sparkfun/SparkFun_GNSS_Flex_System/flex_boards/SparkPNT_GNSS_Flex_Module_LG580P/docs/software_overview.md

## QGNSS Software
!!! warning "Windows Only"
	Currently, the QGNSS software is only available for Windows operating systems.

QGNSS is highly intuitive GNSS evaluation software that is easy to use, personalized, and compatible with leading Quectel technologies. The software allows users to define or apply GNSS product configurations for specific use cases. Saving, restoring, or sharing configurations between different products and users is easy. The software supports product evaluation with a choice of views to observe static and dynamic behavior of the connected a Quectel GNSS receiver.

<article style="text-align: center;" markdown>
[:octicons-download-16:{ .heart } Download the QGNSS Software *(v2.x)* from Quectel](https://www.quectel.com/download/qgnss_v2-0_en/){ .md-button .md-button--primary target="blank" }
</article>

!!! info "System Requirements"
	**Operating System:** Windows

### Connecting to the LG580P
In order to connect to the LG580P properly, users will need to specify the settings of the UART port.

<figure markdown>
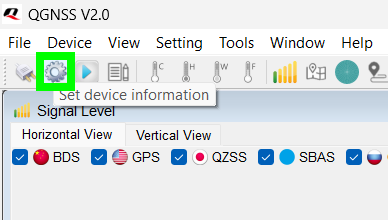
[picture p170: flex_boards/SparkPNT_GNSS_Flex_Module_LG580P/docs/assets/img/hookup_guide/qgnss-uart_settings-button.png]
Configure UART Settings

<figcaption markdown>Click the <kbd>:material-cog:</kbd> button to configure the UART settings.</figcaption>
</figure>

Before users can connect to the LG580P GNSS Flex module, they will need to specify the connection settings in QGNSS. Once configured, users can select the ++"OK"++ button and QGNSS will automatically attempt to connect to the GNSS receiver.

- Select the `LG580P(03)` from the drop-down menu to configure the `Model` of the GNSS receiver being connected.
- Below, is a list of the default settings for `UART` ports of the LG580P. These settings should be selected in the `Device Information` menu, unless configured differently.
- For the `Port`, select the port associated with the connected USB-to-Serial converter.

<figure markdown>
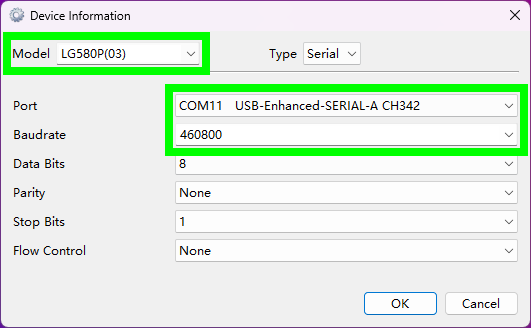
[picture p171: flex_boards/SparkPNT_GNSS_Flex_Module_LG580P/docs/assets/img/hookup_guide/qgnss-uart_settings.png]
UART Settings in QGNSS

<figcaption markdown>Specify the settings for the UART port in QGNSS.</figcaption>
</figure>

### Configure the LG580P
By default, the UART ports are configured to transmit and receive `NMEA 0183` and/or `RTCM 3.x` messages. These messages are generally used for transmitting PNT data; and providing or receiving RTK corrections, respectively. Quectel also implements a system of proprietary messages (`PQTM`) for users to configure the LG580P, following the data format of the `NMEA` protocol.

???+ terminal "Data Format - PQTM Messages"
	The expected structure of the data in the proprietary PQTM messages is shown below:

	<figure markdown>
	NMEA data structure
	<figcaption markdown>The data structure of Quectel messages for the `NMEA` protocol.</figcaption>
	</figure>

	`<Checksum>`:

	- Checksum field follows the checksum delimiter character `*`.
	- Checksum is the 8-bit exclusive OR of all characters in the sentence, including `,` the field delimiter, between but not including the `$` and the `*` delimiters.

	`<CR>` & `<LF>`: Carriage return; followed by a new line

	- Depending on the terminal emulator, these may be options configured in the program settings.
	- Otherwise, users may need to add the `\r` and `\n` characters at the end of the message.

In the QGNSS software, users can click on the ++"Advance"++ button, at the bottom of the `QConsole` window, to configure the settings for the messages sent to the LG580P. Selecting `NMEA` and `CRLF` from the drop-down menu of the **Checksum Type** and **Suffix** options, will automatically calculate and append the `<checksum>` value, carriage return, and line follow to the end of the message entered in the **Data Input** field.

<figure markdown>
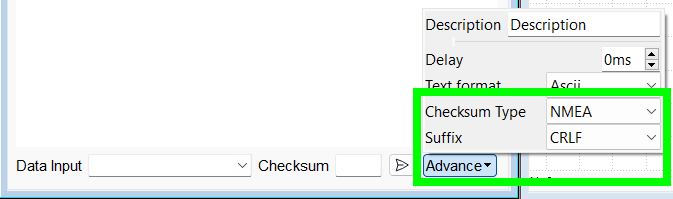
[picture p172: flex_boards/SparkPNT_GNSS_Flex_Module_LG580P/docs/assets/img/hookup_guide/qgnss-message_settings.png]
NMEA message setting

<figcaption markdown>The settings for the messages transmitted from the QConsole.</figcaption>
</figure>

???+ tip "Display the QConsole Toolbar"
	There is a toolbar for the QConsole, which has a bunch of tools that users may find useful. This includes, a search function, scroll-lock button, pause/clear the message feed, etc. To open/close the toolbar inside the QConsole, ++"right-click"++ on the mouse and select the `Show Tool` option from the drop-down menu or utilize the keyboard shortcut: ++ctrl++ + ++q++.

	<figure markdown>
	QConsole Toolbar
	<figcaption markdown>++"Right-click"++ on the mouse and select the `Show Tool` option, inside the QConsole.</figcaption>
	</figure>

??? example "Example - `PQTMCFGUART` Message"
	As an example, try utilizing the `PQTMCFGUART` PQTM message. Enter `$PQTMCFGUART,R*` into the **Data Input** field of the QConsole. DOn't forget to select the `NMEA` and `CRLF` options from ++"Advance"++ settings menu. If entered and configured properly, the value `36` should pop up in the **Checksum** field of the QConsole; then, click on the <kbd>:material-send:</kbd> button to send the message.

	``` bash
	$PQTMCFGUART,R*
	```

	Once the message has been sent, keep a close watch of the messages in the console. It may help to click on the <kbd>:octicons-unlock-16:</kbd> button to disable auto-scrolling, when trying to locate the message response. Additionally, the response may not appear right away, it could be appended to the end of the next data packet, as shown in the image below.

	<figure markdown>
	PQTM demo
	<figcaption markdown>Example of utilizing the Quectel PQTM messages in the QConsole.</figcaption>
	</figure>

### Firmware Update
In the event that users need to update the firmware on the LG580P module, please refer to the instructions in Quectel's [reference manual](./assets/component_documentation/quectel_lg290p03lgx80p03_firmware_upgrade_guide_v1-1.pdf). For the latest firmware, users should reach out to Quectel through their [forum page](https://forums.quectel.com/).

<article style="text-align: center;" markdown>

[Firmware Upgrade Manual](./assets/component_documentation/quectel_lg290p03lgx80p03_firmware_upgrade_guide_v1-1.pdf){ .md-button .md-button--primary target="blank" }

</article>

!!! warning "Synchronization Step"
	In the [reference manual](./assets/component_documentation/quectel_lg290p03lgx80p03_firmware_upgrade_guide_v1-1.pdf), **Step 9** instructs users to wait for a synchronization process. If users refer to an earlier section of the manual, this process requires the LG580P module to receive a `SYNC_WORD1` within 500ms of powering up. Therefore, users must restart the module during the synchronization step. In the QGNSS software *(+v2.1)*, this can be performed with the :material-refresh: reboot button.

	<figure markdown>
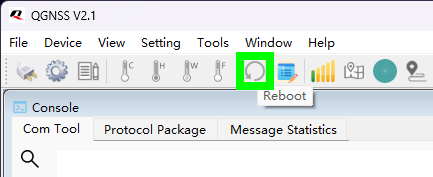
[picture p173: flex_boards/SparkPNT_GNSS_Flex_Module_LG580P/docs/assets/img/hookup_guide/qgnss-reboot_button.png]
Reboot button
	
	<figcaption markdown>Reboot button in the QGNSS software *(v2.1)*.</figcaption>
	</figure>

!!! example "Example - Step-by-Step Instructions"

	1. [Connect to the LG580P](#connecting-to-the-lg580p)
	1. From the **Tools** drop down menu, select **Firmware Update**

		**Tools** > **Firmware Update**

	1. Click the :material-file-send: button to select the receiver firmware
	1. Click to choose the firmware upgrade package whose name is identifiable by the presence of `*.pkg` file extension
	1. Click on the :fontawesome-solid-rotate-backward: button to reboot the GNSS receiver
	1. Click the :material-play: button to start the firmware upgrade process and wait for it to complete
		1. If the GNSS receiver wasn't rebooted prior initializing the upgrade, the process will wait for the synchronization step. The user will then have 20 seconds to manually reboot the GNSS receiver; otherwise, the firmware upgrade process will fail.
		1. Wait for the process to complete
	1. After the firmware upgrade is complete, the module will automatically reboot

## PyGPSClient
As an alternative to QGNSS, we recommend [PyGPSClient](https://github.com/semuconsulting/PyGPSClient) for users with computers that run on MacOS or Linux.

??? info "Resources"
	For additional information, users can refer to the following resources for the PyGPSClient software:

	- :material-github: [GitHub Repository](https://github.com/semuconsulting/PyGPSClient)
	- [Installation Instructions](https://github.com/semuconsulting/PyGPSClient?tab=readme-ov-file#installation)
	- [LG580P Configuration](https://github.com/semuconsulting/PyGPSClient?tab=readme-ov-file#nmeaconfig)
	- [PyPI Project](https://pypi.org/project/pygpsclient/)

### Installation
There are a variety of [installation methods](https://github.com/semuconsulting/PyGPSClient?tab=readme-ov-file#installation) detailed in the GitHub repository's `README.md` file. However, we recommend utilizing the `pip` installation method.

!!! terminal "Installation Commands"
	Depending on how Python is installed on the computer, one of the following commands should allow users to install the software.

	- 
		``` bash
		python3 -m pip install pygpsclient
		```
	- 
		``` bash
		pip install pygpsclient
		```

	??? info "System Requirements"
		This installation method requires an internet connection. Additionally, users will also need administrative privileges *(or root access `sudo`)* for the installation.

### Connecting to the LG580P
Before users can connect to the LG580P GNSS Flex module, they will need to specify the settings of the UART port in PyGPSClient. Once configured, users can select the <kbd>:material-usb:</kbd> button and PyGPSClient will automatically attempt to connect to the GNSS receiver.

- For the `Serial Port`, select the port associated with the GNSS receiver.

<figure markdown>
UART Settings in PyGPSClient
<figcaption markdown>Specify the settings for the UART port in QGNSS.</figcaption>
</figure>

### Terminal Emulator
Another viable option for connecting to the LG580P GNSS Flex module, is to utilize a [terminal emulation program](https://learn.sparkfun.com/tutorials/112). While reading the data sent from the LG580P is relatively trivial, users will need to be more selective when choosing an emulator to configure the LG580P GNSS receiver. This is due to the unique data structure of the proprietary messages that Quectel implements to configure the LG580P *(see the [**Configure the LG580P**](#configure-the-lg580p) section, above)*.

## Arduino Library
The [SparkFun LG290P Quadband RTK GNSS Arduino Library](https://github.com/sparkfun/SparkFun_LG290P_GNSS_Arduino_Library) can be installed from the library manager in the Arduino IDE by searching for:

	SparkFun LG290P Quadband RTK GNSS Arduino Library

<div class="grid" markdown>

<div markdown>

<figure markdown>
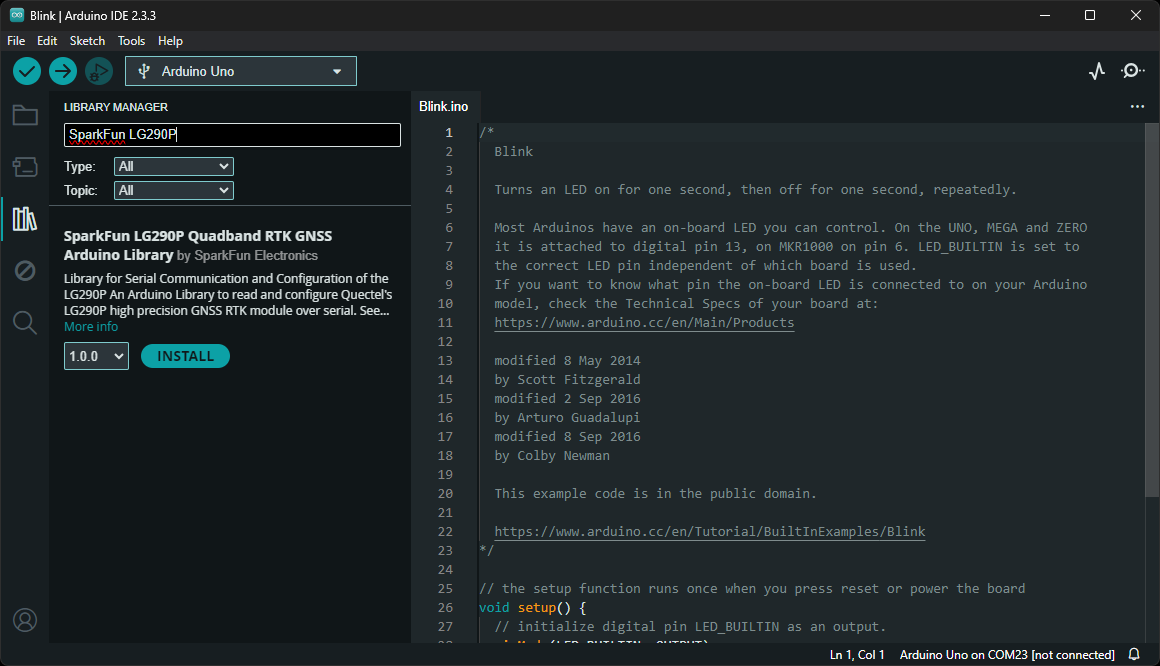
[picture p174: flex_boards/SparkPNT_GNSS_Flex_Module_LG580P/docs/assets/img/hookup_guide/arduino_library.png]
Library listed in the library manager of the Arduino IDE Click to enlarge

<figcaption markdown>The SparkFun LG290P Quadband RTK GNSS Arduino Library in the library manager of the Arduino IDE.</figcaption>
</figure>

</div>

<div markdown>

!!! tip "Manually Download the Arduino Library"
	For users who would like to manually download and install the library, the `*.zip` file can be accessed from the [GitHub repository](https://github.com/sparkfun/SparkFun_LG290P_GNSS_Arduino_Library) or downloaded by clicking the button below.

	<article style="text-align: center;" markdown>
	[:octicons-download-16:{ .heart } Download the Arduino Library](https://github.com/sparkfun/SparkFun_LG290P_GNSS_Arduino_Library/archive/refs/heads/main.zip){ .md-button .md-button--primary }
	</article>

</div>

</div>
