sparkfun/SparkFun_GNSS_Flex_System/docs/modules.md

# All Variants

<!-- Import the component -->
<script type="module" src="https://ajax.googleapis.com/ajax/libs/model-viewer/4.0.0/model-viewer.min.js"></script>

## GNSS *(only)* Modules

<div class="grid cards" style="grid-template-columns: repeat(auto-fit,minmax(8rem,1fr));" markdown>

- **SparkPNT GNSS Flex Module - mosaic-X5**

	---

	<model-viewer src="../SparkPNT_GNSS_Flex_Module_mosaic-X5/assets/3d_model/web_model.glb" camera-controls poster="../SparkPNT_GNSS_Flex_Module_mosaic-X5/assets/3d_model/poster.png" tone-mapping="neutral" shadow-intensity="2" shadow-softness="0.2" camera-orbit="0deg 75deg 0.103m" field-of-view="25.11deg" style="width: 100%; height: 250px;">
	</model-viewer>

	<article style="text-align: center;" markdown>
	[Hookup Guide](./SparkPNT_GNSS_Flex_Module_mosaic-X5/index.md){ .md-button .md-button--primary }

	QR code to product page
	[Purchase from SparkFun :fontawesome-solid-cart-plus:{ .heart }](https://www.sparkfun.com/sparkpnt-gnss-flex-module-mosaic-x5.html){ .md-button .md-button--primary }
	</article>

- **SparkPNT GNSS Flex Module - LG290P**

	---

	<model-viewer src="../SparkPNT_GNSS_Flex_Module_LG290P/assets/3d_model/web_model.glb" camera-controls poster="../SparkPNT_GNSS_Flex_Module_LG290P/assets/3d_model/poster.png" tone-mapping="neutral" shadow-intensity="2" shadow-softness="0.2" camera-orbit="0deg 75deg 0.103m" field-of-view="25.11deg" camera-target="0m 0.8mm 0m" style="width: 100%; height: 250px;">
	</model-viewer>

	<article style="text-align: center;" markdown>
	[Hookup Guide](./SparkPNT_GNSS_Flex_Module_LG290P/index.md){ .md-button .md-button--primary }

	QR code to product page
	[Purchase from SparkFun :fontawesome-solid-cart-plus:{ .heart }](https://www.sparkfun.com/sparkpnt-gnss-flex-module-lg290p.html){ .md-button .md-button--primary }
	</article>

- **SparkPNT GNSS Flex Module - DAN-F10N**

	---

	<model-viewer src="../SparkPNT_GNSS_Flex_Module_DAN-F10N/assets/3d_model/web_model.glb" camera-controls poster="../SparkPNT_GNSS_Flex_Module_DAN-F10N/assets/3d_model/poster.png" tone-mapping="neutral" shadow-intensity="2" shadow-softness="0.2" camera-orbit="90deg 75deg 0.103m" field-of-view="25.11deg" camera-target="0m 0.8mm 0m" style="width: 100%; height: 250px;">
	</model-viewer>

	<article style="text-align: center;" markdown>
	[Hookup Guide](./SparkPNT_GNSS_Flex_Module_DAN-F10N/index.md){ .md-button .md-button--primary }

	QR code to product page
	[Purchase from SparkFun :fontawesome-solid-cart-plus:{ .heart }](https://www.sparkfun.com/sparkpnt-gnss-flex-module-dan-f10n.html){ .md-button .md-button--primary }
	</article>

- **SparkPNT GNSS Flex Module - LG580P**

	---

	<model-viewer src="../SparkPNT_GNSS_Flex_Module_LG580P/assets/3d_model/web_model.glb" camera-controls poster="../SparkPNT_GNSS_Flex_Module_LG580P/assets/3d_model/poster.png" tone-mapping="neutral" shadow-intensity="2" shadow-softness="0.2" camera-orbit="90deg 75deg 0.103m" field-of-view="25.11deg" camera-target="0m 0.8mm 0m" style="width: 100%; height: 250px;">
	</model-viewer>

	<article style="text-align: center;" markdown>
	[Hookup Guide](./SparkPNT_GNSS_Flex_Module_LG580P/index.md){ .md-button .md-button--primary }

	QR code to product page
	[Purchase from SparkFun :fontawesome-solid-cart-plus:{ .heart }](https://www.sparkfun.com/sparkpnt-gnss-flex-module-lg580p.html){ .md-button .md-button--primary }
	</article>

</div>

## GNSS Modules w/ Optional IMU

<div class="grid cards" style="grid-template-columns: repeat(auto-fit,minmax(8rem,1fr));" markdown>

- **SparkPNT GNSS Flex Module - LG290P & IM19 IMU**

	---

	<model-viewer src="../SparkPNT_GNSS_Flex_Module_LG290P-Tilt/assets/3d_model/web_model.glb" camera-controls poster="../SparkPNT_GNSS_Flex_Module_LG290P-Tilt/assets/3d_model/poster.png" tone-mapping="neutral" shadow-intensity="2" shadow-softness="0.2" camera-orbit="90deg 75deg 0.103m" field-of-view="25.11deg" style="width: 100%; height: 250px;">
	</model-viewer>

	<article style="text-align: center;" markdown>
	[Hookup Guide](./SparkPNT_GNSS_Flex_Module_LG290P-Tilt/index.md){ .md-button .md-button--primary }

	QR code to product page
	[Purchase from SparkFun :fontawesome-solid-cart-plus:{ .heart }](https://www.sparkfun.com/sparkpnt-gnss-flex-module-lg290p-im19-imu.html){ .md-button .md-button--primary }
	</article>

- **SparkPNT GNSS Flex Module - ZED-X20P**

	---

	<model-viewer src="../SparkPNT_GNSS_Flex_Module_ZED-X20P-Tilt/assets/3d_model/web_model.glb" camera-controls poster="../SparkPNT_GNSS_Flex_Module_ZED-X20P-Tilt/assets/3d_model/poster.png" tone-mapping="neutral" shadow-intensity="2" shadow-softness="0.2" camera-orbit="0deg 75deg 0.103m" field-of-view="25.11deg" style="width: 100%; height: 250px;">
	</model-viewer>

	<article style="text-align: center;" markdown>
	[Hookup Guide](./SparkPNT_GNSS_Flex_Module_ZED-X20P-Tilt/index.md){ .md-button .md-button--primary }

	<p style="margin-top: .75em; margin-bottom: 0px;" markdown>
	**Purchase from SparkFun :fontawesome-solid-cart-plus:{ .heart }**
	</p>
	<!-- <hr style="margin: 0px;"> -->
	<article class="grid cards" style="margin-top: 0px; grid-template-columns: 1fr 1fr;" markdown>
	<article style="text-align: right;" markdown>

	QR code to product page
	[<span style="text-align: center; font-size: minmax(calc(6px + 0.6vw), 19.2px)">GNSS *(only)*</span>](https://www.sparkfun.com/sparkpnt-gnss-flex-module-zed-x20p.html){ .md-button .md-button--primary style="padding-left: calc(4px + .5vw); padding-right: calc(4px + .5vw);" }

	</article>

	<article style="text-align: left;" markdown>

	QR code to product page
	[<span style="text-align: center; font-size: minmax(calc(6px + 0.6vw), 19.2px)">GNSS + IMU</span>](https://www.sparkfun.com/sparkpnt-gnss-flex-module-zed-x20p-im19-imu.html){ .md-button .md-button--primary style="padding-left: calc(4px + .5vw); padding-right: calc(4px + .5vw);" }

	</article>

	</article>

- **SparkPNT GNSS Flex Module - mosaic-X5 & IM19 IMU**

	---

	<model-viewer src="../SparkPNT_GNSS_Flex_Module_mosaic-X5-Tilt/assets/3d_model/web_model.glb" camera-controls poster="../SparkPNT_GNSS_Flex_Module_mosaic-X5-Tilt/assets/3d_model/poster.png" tone-mapping="neutral" shadow-intensity="2" shadow-softness="0.2" camera-orbit="0deg 75deg 0.103m" field-of-view="25.11deg" style="width: 100%; height: 250px;">
	</model-viewer>

	<article style="text-align: center;" markdown>
	[Hookup Guide](./SparkPNT_GNSS_Flex_Module_mosaic-X5-Tilt/index.md){ .md-button .md-button--primary }

	QR code to product page
	[Purchase from SparkFun :fontawesome-solid-cart-plus:{ .heart }](https://www.sparkfun.com/sparkpnt-gnss-flex-module-mosaic-x5-im19-imu.html){ .md-button .md-button--primary }
	</article>

- **SparkPNT GNSS Flex Module - mosaic-G5 P3**

	---

	<model-viewer src="../SparkPNT_GNSS_Flex_Module_mosaic-G5_P3-Tilt/assets/3d_model/web_model.glb" camera-controls poster="../SparkPNT_GNSS_Flex_Module_mosaic-G5_P3-Tilt/assets/3d_model/poster.png" tone-mapping="neutral" shadow-intensity="2" shadow-softness="0.2" camera-orbit="0deg 75deg 0.103m" field-of-view="25.11deg" style="width: 100%; height: 250px;">
	</model-viewer>

	<article style="text-align: center;" markdown>
	[Hookup Guide](./SparkPNT_GNSS_Flex_Module_mosaic-G5_P3-Tilt/index.md){ .md-button .md-button--primary }

	<p style="margin-top: .75em; margin-bottom: 0px;" markdown>
	**Purchase from SparkFun :fontawesome-solid-cart-plus:{ .heart }**
	</p>
	<!-- <hr style="margin: 0px;"> -->
	<article class="grid cards" style="margin-top: 0px; grid-template-columns: 1fr 1fr;" markdown>
	<article style="text-align: right;" markdown>

	QR code to product page
	[<span style="text-align: center; font-size: minmax(calc(6px + 0.6vw), 19.2px)">GNSS *(only)*</span>](https://www.sparkfun.com/sparkpnt-gnss-flex-module-mosaic-g5-p3.html){ .md-button .md-button--primary style="padding-left: calc(4px + .5vw); padding-right: calc(4px + .5vw);" }

	</article>

	<article style="text-align: left;" markdown>

	QR code to product page
	[<span style="text-align: center; font-size: minmax(calc(6px + 0.6vw), 19.2px)">GNSS + IMU</span>](https://www.sparkfun.com/sparkpnt-gnss-flex-module-mosaic-g5-p3-im19-imu.html){ .md-button .md-button--primary style="padding-left: calc(4px + .5vw); padding-right: calc(4px + .5vw);" }

	</article>

	</article>

</div>
