sparkfun/SparkFun_GNSS_Flex_System/docs/resources.md

## GNSS Flex Modules

### GNSS Module *(only)*

<div class="grid cards" style="grid-template-columns: repeat(auto-fit,minmax(8rem,1fr));" markdown>

- **mosaic-X5**

	---

	- :material-folder-cog: Design Files:
		- :fontawesome-solid-file-pdf: [Schematic](SparkPNT_GNSS_Flex_Module_mosaic-X5/assets/board_files/schematic.pdf)
		- :fontawesome-solid-file-pdf: [Board Dimensions](SparkPNT_GNSS_Flex_Module_mosaic-X5/assets/board_files/dimensions.pdf)
		- :material-folder-zip: [KiCad Files](SparkPNT_GNSS_Flex_Module_mosaic-X5/assets/board_files/kicad_files.zip)
		- :material-cube-outline: [STEP File](SparkPNT_GNSS_Flex_Module_mosaic-X5/assets/3d_model/cad_model.step)
	- Component Documentation
		- :fontawesome-solid-file-pdf: [mosaic-X5 Datasheet](SparkPNT_GNSS_Flex_Module_mosaic-X5/assets/component_documentation/mosaic_hardware_manual_v1.11.0.pdf)
		- :fontawesome-solid-file-pdf: [mosaic-X5 Brochure](SparkPNT_GNSS_Flex_Module_mosaic-X5/assets/component_documentation/Septentrio_mosaic-X5_LR.pdf)
		- :fontawesome-solid-file-pdf: [Firmware Manual *(v4.15.0)*](SparkPNT_GNSS_Flex_Module_mosaic-X5/assets/component_documentation/firmware/mosaic-X5_Firmware_v4.15.0_Reference_Guide.pdf)
	- :material-youtube: [Product Showcase](https://youtu.be/r-bhOLv4zsk)

- **LG290P**

	---

	- :material-folder-cog: Design Files:
		- :fontawesome-solid-file-pdf: [Schematic](SparkPNT_GNSS_Flex_Module_LG290P/assets/board_files/schematic.pdf)
		- :fontawesome-solid-file-pdf: [Board Dimensions](SparkPNT_GNSS_Flex_Module_LG290P/assets/board_files/dimensions.pdf)
		- :material-folder-zip: [KiCad Files](SparkPNT_GNSS_Flex_Module_LG290P/assets/board_files/kicad_files.zip)
		- :material-cube-outline: [STEP File](SparkPNT_GNSS_Flex_Module_LG290P/assets/3d_model/cad_model.step)
	- Component Documentation
		- :fontawesome-solid-file-pdf: [Product Specifications](SparkPNT_GNSS_Flex_Module_LG290P/assets/component_documentation/Quectel_LG290P03_GNSS_Module_Specification_V1.2.pdf)
		- :fontawesome-solid-file-pdf: [Protocol Specification](SparkPNT_GNSS_Flex_Module_LG290P/assets/component_documentation/quectel_lg290p03lgx80p03_gnss_protocol_specification_v1-1.pdf)
		- :fontawesome-solid-file-pdf: [Hardware Design](SparkPNT_GNSS_Flex_Module_LG290P/assets/component_documentation/quectel_lg290p03_hardware_design_v1-1.pdf)
		- :fontawesome-solid-file-pdf: [Firmware Upgrade Guide](SparkPNT_GNSS_Flex_Module_LG290P/assets/component_documentation/quectel_lg290p03lgx80p03_firmware_upgrade_guide_v1-1.pdf)
		- :fontawesome-solid-file-pdf: [Application Note - RTK Corrections](SparkPNT_GNSS_Flex_Module_LG290P/assets/component_documentation/quectel_lg290p03lgx80p03_rtk_application_note_v1-1.pdf)
		- :fontawesome-solid-file-pdf: [Application Note - Base Station](SparkPNT_GNSS_Flex_Module_LG290P/assets/component_documentation/quectel_lg290p03lgx80p_series_base_station_mode_application_note_v1-1.pdf)
	- :material-youtube: [Product Showcase](https://youtu.be/r-bhOLv4zsk)

- **DAN-F10N**

	---

	- :material-folder-cog: Design Files:
		- :fontawesome-solid-file-pdf: [Schematic](SparkPNT_GNSS_Flex_Module_DAN-F10N/assets/board_files/schematic.pdf)
		- :fontawesome-solid-file-pdf: [Board Dimensions](SparkPNT_GNSS_Flex_Module_DAN-F10N/assets/board_files/dimensions.pdf)
		- :material-folder-zip: [KiCad Files](SparkPNT_GNSS_Flex_Module_DAN-F10N/assets/board_files/kicad_files.zip)
		- :material-cube-outline: [STEP File](SparkPNT_GNSS_Flex_Module_DAN-F10N/assets/3d_model/cad_model.step)
	- Component Documentation
		- :fontawesome-solid-file-pdf: [Datasheet](https://content.u-blox.com/sites/default/files/documents/DAN-F10N_DataSheet_UBXDOC-963802114-13074.pdf)
		- :fontawesome-solid-file-pdf: [Product Summary](https://content.u-blox.com/sites/default/files/documents/DAN-F10N_ProductSummary_UBXDOC-963802114-13162.pdf)
		- :fontawesome-solid-file-pdf: [Integration Manual](https://content.u-blox.com/sites/default/files/documents/DAN-F10N_IntegrationManual_UBXDOC-963802114-13252.pdf)

- **LG580P**

	---

	- :material-folder-cog: Design Files:
		- :fontawesome-solid-file-pdf: [Schematic](SparkPNT_GNSS_Flex_Module_LG580P/assets/board_files/schematic.pdf)
		- :fontawesome-solid-file-pdf: [Board Dimensions](SparkPNT_GNSS_Flex_Module_LG580P/assets/board_files/dimensions.pdf)
		- :material-folder-zip: [KiCad Files](SparkPNT_GNSS_Flex_Module_LG580P/assets/board_files/kicad_files.zip)
		- :material-cube-outline: [STEP File](SparkPNT_GNSS_Flex_Module_LG580P/assets/3d_model/cad_model.step)
	- Component Documentation
		- :fontawesome-solid-file-pdf: [Product Specifications](SparkPNT_GNSS_Flex_Module_LG580P/assets/component_documentation/Quectel_LG580P03_GNSS_Module_Specification_V1.0.pdf)
		- :fontawesome-solid-file-pdf: [Protocol Specification](SparkPNT_GNSS_Flex_Module_LG580P/assets/component_documentation/quectel_lg290p03lgx80p03_gnss_protocol_specification_v1-1.pdf)
		- :fontawesome-solid-file-pdf: [Hardware Design](SparkPNT_GNSS_Flex_Module_LG580P/assets/component_documentation/quectel_lg580p03_hardware_design_v1-0.pdf)
		- :fontawesome-solid-file-pdf: [Firmware Upgrade Guide](SparkPNT_GNSS_Flex_Module_LG580P/assets/component_documentation/quectel_lg290p03lgx80p03_firmware_upgrade_guide_v1-1.pdf)
		- :fontawesome-solid-file-pdf: [Application Note - RTK Corrections](SparkPNT_GNSS_Flex_Module_LG580P/assets/component_documentation/quectel_lg290p03lgx80p03_rtk_application_note_v1-1.pdf)
		- :fontawesome-solid-file-pdf: [Application Note - Base Station](SparkPNT_GNSS_Flex_Module_LG580P/assets/component_documentation/quectel_lg290p03lgx80p_series_base_station_mode_application_note_v1-1.pdf)
		- :fontawesome-solid-file-pdf: [Application Note - Heading](SparkPNT_GNSS_Flex_Module_LG580P/assets/component_documentation/quectel_lg580p_series_dual-antenna_heading_application_note_v1-0.pdf)

</div>

## GNSS Module w/ Optional IMU

<div class="grid cards" style="grid-template-columns: repeat(auto-fit,minmax(8rem,1fr));" markdown>

- **LG290P**

	---

	- :material-folder-cog: Design Files:
		- :fontawesome-solid-file-pdf: [Schematic](SparkPNT_GNSS_Flex_Module_LG290P-Tilt/assets/board_files/schematic.pdf)
		- :fontawesome-solid-file-pdf: [Board Dimensions](SparkPNT_GNSS_Flex_Module_LG290P-Tilt/assets/board_files/dimensions.pdf)
		- :material-folder-zip: [KiCad Files](SparkPNT_GNSS_Flex_Module_LG290P-Tilt/assets/board_files/kicad_files.zip)
		- :material-cube-outline: [STEP File](SparkPNT_GNSS_Flex_Module_LG290P-Tilt/assets/3d_model/cad_model.step)
	- Component Documentation
		- LG290P GNSS Module
			- :fontawesome-solid-file-pdf: [Product Specifications](SparkPNT_GNSS_Flex_Module_LG290P-Tilt/assets/component_documentation/Quectel_LG290P03_GNSS_Module_Specification_V1.2.pdf)
			- :fontawesome-solid-file-pdf: [Protocol Specification](SparkPNT_GNSS_Flex_Module_LG290P-Tilt/assets/component_documentation/quectel_lg290p03lgx80p03_gnss_protocol_specification_v1-1.pdf)
			- :fontawesome-solid-file-pdf: [Hardware Design](SparkPNT_GNSS_Flex_Module_LG290P-Tilt/assets/component_documentation/quectel_lg290p03_hardware_design_v1-1.pdf)
			- :fontawesome-solid-file-pdf: [Firmware Upgrade Guide](SparkPNT_GNSS_Flex_Module_LG290P-Tilt/assets/component_documentation/quectel_lg290p03lgx80p03_firmware_upgrade_guide_v1-1.pdf)
			- :fontawesome-solid-file-pdf: [Application Note - RTK Corrections](SparkPNT_GNSS_Flex_Module_LG290P-Tilt/assets/component_documentation/quectel_lg290p03lgx80p03_rtk_application_note_v1-1.pdf)
			- :fontawesome-solid-file-pdf: [Application Note - Base Station](SparkPNT_GNSS_Flex_Module_LG290P-Tilt/assets/component_documentation/quectel_lg290p03lgx80p_series_base_station_mode_application_note_v1-1.pdf)
		- IM19 Attitude Module
			- :fontawesome-solid-file-pdf: [Datasheet](./assets/component_documentation/IM19.pdf)
			- :fontawesome-solid-file-pdf: [Integration Guide](./assets/component_documentation/IM19EI_v1.4.1.pdf)

- **ZED-X20P**

	---

	- :material-folder-cog: Design Files:
		- :fontawesome-solid-file-pdf: [Schematic](SparkPNT_GNSS_Flex_Module_ZED-X20P-Tilt/assets/board_files/schematic.pdf)
		- :fontawesome-solid-file-pdf: [Board Dimensions](SparkPNT_GNSS_Flex_Module_ZED-X20P-Tilt/assets/board_files/dimensions.pdf)
		- :material-folder-zip: [KiCad Files](SparkPNT_GNSS_Flex_Module_ZED-X20P-Tilt/assets/board_files/kicad_files.zip)
		- :material-cube-outline: [STEP File](SparkPNT_GNSS_Flex_Module_ZED-X20P-Tilt/assets/3d_model/cad_model.step)
	- Component Documentation
		- ZED-X20P GNSS Module
			- :fontawesome-solid-file-pdf: [Datasheet](https://www.u-blox.com/sites/default/files/documents/ZED-X20P-00B_DataSheet_UBXDOC-963802114-12690.pdf)
			- :fontawesome-solid-file-pdf: [Product Summary](https://www.u-blox.com/sites/default/files/documents/ZED-X20P_ProductSummary_UBXDOC-304424225-18238.pdf)
			- :fontawesome-solid-file-pdf: [Integration Manual](https://www.u-blox.com/sites/default/files/documents/ZED-X20P_IntegrationManual_UBXDOC-963802114-12901.pdf)
			- Application Notes
				- :fontawesome-solid-file-pdf: [GPS L5 Configuration](https://www.u-blox.com/sites/default/files/documents/GPS-L5-configuration_AppNote_UBX-21038688.pdf)
			- Firmware *(HPG 2.00)*
				- :octicons-file-binary-16: [Firmware File](https://content.u-blox.com/sites/default/files/2025-05/UBX_20_HPG200_ZED-X20P.cbadd47b7f0eb6224338ae146252eedb.bin)
				- :fontawesome-solid-file-pdf: [Interface Manual](https://www.u-blox.com/sites/default/files/documents/u-blox-20-HPG-2.00_InterfaceDescription_UBXDOC-304424225-19888.pdf)
				- :fontawesome-solid-file-pdf: [Release Notes](https://www.u-blox.com/sites/default/files/documents/HPG200_RN_UBXDOC-304424225-19895.pdf)
		- IM19 Attitude Module
			- :fontawesome-solid-file-pdf: [Datasheet](./assets/component_documentation/IM19.pdf)
			- :fontawesome-solid-file-pdf: [Integration Guide](./assets/component_documentation/IM19EI_v1.4.1.pdf)

- **mosaic-X5**

	---

	- :material-folder-cog: Design Files:
		- :fontawesome-solid-file-pdf: [Schematic](SparkPNT_GNSS_Flex_Module_mosaic-X5-Tilt/assets/board_files/schematic.pdf)
		- :fontawesome-solid-file-pdf: [Board Dimensions](SparkPNT_GNSS_Flex_Module_mosaic-X5-Tilt/assets/board_files/dimensions.pdf)
		- :material-folder-zip: [KiCad Files](SparkPNT_GNSS_Flex_Module_mosaic-X5-Tilt/assets/board_files/kicad_files.zip)
		- :material-cube-outline: [STEP File](SparkPNT_GNSS_Flex_Module_mosaic-X5-Tilt/assets/3d_model/cad_model.step)
	- Component Documentation
		- mosaic-X5 GNSS Module
			- :fontawesome-solid-file-pdf: [mosaic-X5 Datasheet](SparkPNT_GNSS_Flex_Module_mosaic-X5-Tilt/assets/component_documentation/mosaic_hardware_manual_v1.11.0.pdf)
			- :fontawesome-solid-file-pdf: [mosaic-X5 Brochure](SparkPNT_GNSS_Flex_Module_mosaic-X5-Tilt/assets/component_documentation/Septentrio_mosaic-X5_LR.pdf)
			- :fontawesome-solid-file-pdf: [Firmware Manual *(v4.15.0)*](SparkPNT_GNSS_Flex_Module_mosaic-X5-Tilt/assets/component_documentation/firmware/mosaic-X5_Firmware_v4.15.0_Reference_Guide.pdf)
		- IM19 Attitude Module
			- :fontawesome-solid-file-pdf: [Datasheet](./assets/component_documentation/IM19.pdf)
			- :fontawesome-solid-file-pdf: [Integration Guide](./assets/component_documentation/IM19EI_v1.4.1.pdf)

- **mosaic-G5 P3**

	---

	- :material-folder-cog: Design Files:
		- :fontawesome-solid-file-pdf: [Schematic](SparkPNT_GNSS_Flex_Module_mosaic-G5_P3-Tilt/assets/board_files/schematic.pdf)
		- :fontawesome-solid-file-pdf: [Board Dimensions](SparkPNT_GNSS_Flex_Module_mosaic-G5_P3-Tilt/assets/board_files/dimensions.pdf)
		- :material-folder-zip: [KiCad Files](SparkPNT_GNSS_Flex_Module_mosaic-G5_P3-Tilt/assets/board_files/kicad_files.zip)
		- :material-cube-outline: [STEP File](SparkPNT_GNSS_Flex_Module_mosaic-G5_P3-Tilt/assets/3d_model/cad_model.step)
	- Component Documentation
		- mosaic-G5 P3 GNSS Module
			- :fontawesome-solid-file-pdf: [mosaic-G5 P3 Datasheet](SparkPNT_GNSS_Flex_Module_mosaic-G5_P3-Tilt/assets/component_documentation/mosaic-g5_hardware_manual_v1.1.1.pdf)
			- :fontawesome-solid-file-pdf: [mosaic-G5 P3 Brochure](SparkPNT_GNSS_Flex_Module_mosaic-G5_P3-Tilt/assets/component_documentation/Septentrio_mosaic-G5_P3_&_P3H.pdf)
			- :fontawesome-solid-file-pdf: [Firmware Manual *(v1.0.1)*](SparkPNT_GNSS_Flex_Module_mosaic-G5_P3-Tilt/assets/component_documentation/firmware/v1.0.1/mosaic-G5 Firmware v1.0.1 Reference Guide.pdf)
		- IM19 Attitude Module
			- :fontawesome-solid-file-pdf: [Datasheet](./assets/component_documentation/IM19.pdf)
			- :fontawesome-solid-file-pdf: [Integration Guide](./assets/component_documentation/IM19EI_v1.4.1.pdf)

</div>

## Carrier Boards

<div class="grid cards" style="grid-template-columns: repeat(auto-fit,minmax(8rem,1fr));" markdown>

- **GNSS Flex pHAT**

	---

	- :material-folder-cog: Design Files:
		- :fontawesome-solid-file-pdf: [Schematic](SparkFun_GNSS_Flex_pHAT/assets/board_files/schematic.pdf)
		- :fontawesome-solid-file-pdf: [Board Dimensions](SparkFun_GNSS_Flex_pHAT/assets/board_files/dimensions.pdf)
		- :material-folder-zip: [KiCad Files](SparkFun_GNSS_Flex_pHAT/assets/board_files/kicad_files.zip)
		- :material-cube-outline: [STEP File](SparkFun_GNSS_Flex_pHAT/assets/3d_model/cad_model.step)
	- Design Specifications:
		- [Design Requirements](https://datasheets.raspberrypi.com/hat/hat-plus-specification.pdf)
		- [Mechanical Specifications](https://raw.githubusercontent.com/raspberrypi/hats/refs/heads/master/hat-board-mechanical.pdf)
	- :material-youtube: [Product Showcase](https://youtu.be/r-bhOLv4zsk)
	- :material-github: [Hardware Repo](https://github.com/sparkfun/SparkFun_GNSS_Flex_pHAT)

- **GNSS Flex Breakout Board**

	---

	- :material-folder-cog: Design Files:
		- :fontawesome-solid-file-pdf: [Schematic](SparkFun_GNSS_Flex_Breakout/assets/board_files/schematic.pdf)
		- :fontawesome-solid-file-pdf: [Board Dimensions](SparkFun_GNSS_Flex_Breakout/assets/board_files/dimensions.pdf)
		- :material-folder-zip: [KiCad Files](SparkFun_GNSS_Flex_Breakout/assets/board_files/kicad_files.zip)
		- :material-cube-outline: [STEP File](SparkFun_GNSS_Flex_Breakout/assets/3d_model/cad_model.step)
	- Component Documentation
		- :fontawesome-solid-file-pdf: [CH342 Datasheet](SparkFun_GNSS_Flex_Breakout/assets/component_documentation/CH342%20Datasheet.pdf)
		- :fontawesome-solid-file-pdf: [JST-GH Datasheet](SparkFun_GNSS_Flex_Breakout/assets/component_documentation/JST-GH_datasheet.pdf)
		- :fontawesome-solid-file-pdf: [JST-SH Datasheet](SparkFun_GNSS_Flex_Breakout/assets/component_documentation/JST-SH_datasheet.pdf)
	- :material-github: [Hardware Repo](https://github.com/sparkfun/SparkFun_GNSS_Flex_Breakout)

</div>

## :sfe: Additional Resources

- :material-account-supervisor: [SparkFun Technical Assistance](https://www.sparkfun.com/technical_assistance)
- :material-github: [GitHub Repository](https://github.com/sparkfun/SparkFun_GNSS_Flex_System)
