sparkfun/SparkFun_GNSS_Flex_System/flex_boards/SparkPNT_GNSS_Flex_Module_DAN-F10N/docs/resources.md

## Product Resources

- Product Pages
	- :sfe: [SparkPNT GNSS Flex Module - DAN-F10N](https://www.sparkfun.com/sparkpnt-gnss-flex-module-dan-f10n.html)
	- :sfe: [SparkFun GNSS Flex pHAT - DAN-F10N](https://www.sparkfun.com/sparkfun-gnss-flex-phat-dan-f10n.html)
- :material-folder-cog: Design Files:
	- :fontawesome-solid-file-pdf: [Board Dimensions](./assets/board_files/dimensions.pdf)
	- :fontawesome-solid-file-pdf: [Schematic](./assets/board_files/schematic.pdf)
	- :material-folder-zip: [KiCad Files](./assets/board_files/kicad_files.zip)
	- :material-cube-outline: [STEP File](./assets/3d_model/cad_model.step)
- :fontawesome-solid-computer: [u-center 2 Software](https://www.u-blox.com/en/product/u-center)
	- :material-cloud-download: [Download](https://u-center2-updates.u-blox.com/u-center2-installer.exe)
	- :material-book-open-variant: [User Manual](https://www.u-blox.com/en/info/u-center-2-user-guide)
- Component Documentation
	- DAN-F10N GNSS Module:
		- :fontawesome-solid-file-pdf: [Datasheet](https://content.u-blox.com/sites/default/files/documents/DAN-F10N_DataSheet_UBXDOC-963802114-13074.pdf)
		- :fontawesome-solid-file-pdf: [Product Summary](https://content.u-blox.com/sites/default/files/documents/DAN-F10N_ProductSummary_UBXDOC-963802114-13162.pdf)
		- :fontawesome-solid-file-pdf: [Integration Manual](https://content.u-blox.com/sites/default/files/documents/DAN-F10N_IntegrationManual_UBXDOC-963802114-13252.pdf)
- :material-github: [GitHub Repository](https://github.com/sparkfun/SparkFun_GNSS_Flex_System)

## 🏭&nbsp;Manufacturer's Resources
u-blox also provides great resources for the DAN-F10N GNSS receiver:

- [DAN-F10N Product Page](https://www.u-blox.com/en/product/dan-f10n-module)
- :material-youtube: [u-blox YouTube Channel](https://www.youtube.com/@ublox)
	- :material-playlist-play: [Playlist: u-center 2](https://www.youtube.com/playlist?list=PLSzSoRUA4EXuo9NTsbTnK84MiKvbVCEKt)
- :material-head-question: [Support Page](https://portal.u-blox.com/s/)
- :material-folder-search: [Product Documentation](https://www.u-blox.com/en/product-resources?legacy=Current)
	- :material-head-lightbulb: [PNT Technologies](https://www.u-blox.com/en/positioning-and-location)
	- :fontawesome-solid-computer: [u-center 2 Software](https://www.u-blox.com/en/u-center-2)
		- :material-youtube: [Webinar](https://www.youtube.com/watch?v=ZYttFyZ_7Uo)
		- :material-school: [Tutorials](https://www.u-blox.com/en/u-center2-tutorials)
