sparkfun/SparkFun_GNSS_Flex_System/flex_boards/SparkPNT_GNSS_Flex_Module_LG290P-Tilt/docs/resources.md

## Product Resources

- Product Pages
	- :sfe: [SparkPNT GNSS Flex Module - LG290P & IM19](https://www.sparkfun.com/sparkpnt-gnss-flex-module-lg290p-im19-imu.html)
	- :sfe: [SparkFun GNSS Flex pHAT - LG290P & IM19](https://www.sparkfun.com/sparkfun-gnss-flex-phat-lg290p-im19-imu.html)
- :material-folder-cog: Design Files:
	- :fontawesome-solid-file-pdf: [Schematic](./assets/board_files/schematic.pdf)
	- :fontawesome-solid-file-pdf: [Board Dimensions](./assets/board_files/dimensions.pdf)
	- :material-folder-zip: [KiCad Files](./assets/board_files/kicad_files.zip)
	- :material-cube-outline: [STEP File](./assets/3d_model/cad_model.step)
- :fontawesome-solid-computer: [QGNSS Software *(v2.x)*](https://www.quectel.com/download/qgnss_v2-0_en/)
- Component Documentation
	- LG290P GNSS Receiver
		- :fontawesome-solid-file-pdf: [Product Specifications](./assets/component_documentation/Quectel_LG290P03_GNSS_Module_Specification_V1.2.pdf)
		- :fontawesome-solid-file-pdf: [Protocol Specification](./assets/component_documentation/quectel_lg290p03lgx80p03_gnss_protocol_specification_v1-1.pdf)
		- :fontawesome-solid-file-pdf: [Hardware Design](./assets/component_documentation/quectel_lg290p03_hardware_design_v1-1.pdf)
		- :fontawesome-solid-file-pdf: [Application Note - RTK Corrections](./assets/component_documentation/quectel_lg290p03lgx80p03_rtk_application_note_v1-1.pdf)
		- :fontawesome-solid-file-pdf: [Application Note - Base Station](./assets/component_documentation/quectel_lg290p03lgx80p_series_base_station_mode_application_note_v1-1.pdf)
		- :fontawesome-solid-file-pdf: [Firmware Upgrade Guide](./assets/component_documentation/quectel_lg290p03lgx80p03_firmware_upgrade_guide_v1-1.pdf)
	- IM19 Attitude Module
		- :fontawesome-solid-file-pdf: [Datasheet](../assets/component_documentation/IM19.pdf)
		- :fontawesome-solid-file-pdf: [Integration Guide](../assets/component_documentation/IM19EI_v1.4.1.pdf)
- :material-github: [GitHub Repository](https://github.com/sparkfun/SparkFun_GNSS_Flex_System)

## 🏭&nbsp;Manufacturer's Resources
Quectel also provides great resources for the LG290P GNSS receiver:

- :material-web: [Product Webpage](https://www.quectel.com/product/gnss-lg290p/)
- :material-help-box: [Quectel Forum](https://forums.quectel.com/)
- :material-account-supervisor: [Technical Support](https://www.quectel.com/tech-support/)
- :material-cloud-download: [Download Zone](https://www.quectel.com/download-zone/?_sft_product_cat=gnss-modules-standalone)
- :material-newspaper-variant: [Resource Library](https://www.quectel.com/library?_sft_topic=gnss)

Feyman Inc. also provides some resources for the IM19 attitude module:

- :material-web: [IM19 Product Page](https://global.feymani.com/product/attitede/im19ee/)
	- :material-newspaper-variant: [Documentation](https://global.feymani.com/document/)
- :material-web: [IM19 Product Page](http://feymani.com/en/show-53-2-1.html) *(alternate website)*
- :material-youtube: [Feyman Inc. YouTube Channel](https://www.youtube.com/@FeymanIncFMI)
