sparkfun/SparkFun_GNSS_Flex_System/flex_boards/SparkPNT_GNSS_Flex_Module_LG580P/docs/resources.md

## Product Resources

- Product Pages
	- :sfe: [SparkPNT GNSS Flex Module - LG580P](https://www.sparkfun.com/sparkpnt-gnss-flex-module-lg580p.html)
	- :sfe: [SparkFun GNSS Flex pHAT - LG580P](https://www.sparkfun.com/sparkfun-gnss-flex-phat-lg580p.html)
- :material-folder-cog: Design Files:
	- :fontawesome-solid-file-pdf: [Board Dimensions](./assets/board_files/dimensions.pdf)
	- :fontawesome-solid-file-pdf: [Schematic](./assets/board_files/schematic.pdf)
	- :material-folder-zip: [KiCad Files](./assets/board_files/kicad_files.zip)
	- :material-cube-outline: [STEP File](./assets/3d_model/cad_model.step)
- :fontawesome-solid-computer: [QGNSS Software *(v2.x)*](https://www.quectel.com/download/qgnss_v2-0_en/)
- Component Documentation
	- :fontawesome-solid-file-pdf: [Product Specifications](./assets/component_documentation/Quectel_LG580P03_GNSS_Module_Specification_V1.0.pdf)
	- :fontawesome-solid-file-pdf: [Protocol Specification](./assets/component_documentation/quectel_lg290p03lgx80p03_gnss_protocol_specification_v1-1.pdf)
	- :fontawesome-solid-file-pdf: [Hardware Design](./assets/component_documentation/quectel_lg580p03_hardware_design_v1-0.pdf)
	- :fontawesome-solid-file-pdf: [Firmware Upgrade Guide](./assets/component_documentation/quectel_lg290p03lgx80p03_firmware_upgrade_guide_v1-1.pdf)
	- :fontawesome-solid-file-pdf: [Application Note - RTK Corrections](./assets/component_documentation/quectel_lg290p03lgx80p03_rtk_application_note_v1-1.pdf)
	- :fontawesome-solid-file-pdf: [Application Note - Base Station](./assets/component_documentation/quectel_lg290p03lgx80p_series_base_station_mode_application_note_v1-1.pdf)
	- :fontawesome-solid-file-pdf: [Application Note - Heading](./assets/component_documentation/quectel_lg580p_series_dual-antenna_heading_application_note_v1-0.pdf)
- :material-github: [GitHub Repository](https://github.com/sparkfun/SparkFun_GNSS_Flex_System)

## 🏭&nbsp;Manufacturer's Resources
Quectel also provides great resources for the LG580P GNSS receiver:

- :material-web: [Product Webpage](https://www.quectel.com/product/gnss-lg580p-03/)
- :material-help-box: [Quectel Forum](https://forums.quectel.com/)
- :material-account-supervisor: [Technical Support](https://www.quectel.com/tech-support/)
- :material-cloud-download: [Download Zone](https://www.quectel.com/download-zone/?_sft_product_cat=gnss-modules-standalone)
- :material-newspaper-variant: [Resource Library](https://www.quectel.com/library?_sft_topic=gnss)
