sparkfun/SparkFun_GNSS_Flex_System/flex_boards/SparkPNT_GNSS_Flex_Module_mosaic-G5_P3-Tilt/docs/resources.md

## Product Resources

<div class="grid" markdown>

<div markdown>

- Product Pages
	- :sfe: [SparkPNT GNSS Flex Module - ZED-X20P](https://www.sparkfun.com/sparkpnt-gnss-flex-module-zed-x20p.html)
	- :sfe: [SparkPNT GNSS Flex Module - ZED-X20P & IM19](https://www.sparkfun.com/sparkpnt-gnss-flex-module-zed-x20p-im19-imu.html)
	- :sfe: [SparkFun GNSS Flex pHAT - ZED-X20P](https://www.sparkfun.com/sparkfun-gnss-flex-phat-zed-x20p.html)
	- :sfe: [SparkFun GNSS Flex pHAT - ZED-X20P & IM19](https://www.sparkfun.com/sparkfun-gnss-flex-phat-zed-x20p-im19-imu.html)
- :material-folder-cog: Design Files:
	- :fontawesome-solid-file-pdf: [Board Dimensions](./assets/board_files/dimensions.pdf)
	- :fontawesome-solid-file-pdf: [Schematic](./assets/board_files/schematic.pdf)
	- :material-folder-zip: [KiCad Files](./assets/board_files/kicad_files.zip)
	- :material-cube-outline: [STEP File](./assets/3d_model/cad_model.step)

</div>

<div markdown>

- [RXTools Software Suite](https://www.septentrio.com/en/products/gps-gnss-receiver-software/rxtools)
- Component Documentation
	-  mosaic-G5 P3 GNSS Receiver
		- :fontawesome-solid-file-pdf: [mosaic-G5 P3 Datasheet](./assets/component_documentation/mosaic-g5_hardware_manual_v1.1.1.pdf)
		- :fontawesome-solid-file-pdf: [mosaic-G5 P3 Brochure](./assets/component_documentation/Septentrio_mosaic-G5_P3_&_P3H.pdf)
		- :fontawesome-solid-file-pdf: [Firmware Manual *(v1.0.1)*](./assets/component_documentation/firmware/v1.0.1/mosaic-G5%20Firmware%20v1.0.1%20Reference%20Guide.pdf)
	- IM19 Attitude Module
		- :fontawesome-solid-file-pdf: [Datasheet](../assets/component_documentation/IM19.pdf)
		- :fontawesome-solid-file-pdf: [Integration Guide](../assets/component_documentation/IM19EI_v1.4.1.pdf)
- :material-github: [GitHub Repository](https://github.com/sparkfun/SparkFun_GNSS_Flex_System)

</div>

</div>

## 🏭&nbsp;Manufacturer's Resources
Septentrio also provides great resources for the mossaic-X5 GNSS receiver:

- [mosaic-G5 P3 Product Page](https://www.septentrio.com/en/products/gnss-receivers/gnss-receiver-modules/mosaic-G5-P3)
- :material-youtube: [Septentrio YouTube Channel](https://www.youtube.com/channel/UCrA9wMw1y1f-KeOnnhq4lrA/feed)
- [Support Page](https://www.septentrio.com/en/support)
	- :material-head-question: [Technical Support Portal](https://customersupport.septentrio.com/s/)
		- :material-head-lightbulb: [Knowledge Base](https://customersupport.septentrio.com/s/topiccatalog)
			- [**mosaic-G5:** Product variant differentiation (P1/P3/P3H)](https://customersupport.septentrio.com/s/article/mosaic-G5-Variant-differentiation)
			- [**mosaic-G5:** Getting started guide](https://customersupport.septentrio.com/s/article/mosaic-G5-getting-started)
			- [**mosaic-G5:** Bluetooth (HC-06) dongle integration](https://customersupport.septentrio.com/s/article/mosaic-G5-bluetooth-dongle-integration)
			- [**mosaic-G5:** step-by-step guide on how to setup an RTK capable mosaic-G5 receiver](https://customersupport.septentrio.com/s/article/mosaic-G5-getting-started-RTK-setup-mosaic-G5)
			- [**mosaic-G5:** Logging data on mosaic-G5](https://customersupport.septentrio.com/s/article/mosaic-G5-logging-data-on-G5)
			- [**CLI Chapter 1:** How to access the Command Line Interface?](https://customersupport.septentrio.com/s/article/How-to-access-the-Command-Line-Interface)
			- [**CLI Chapter 2:** Command Line Interface description](https://customersupport.septentrio.com/s/article/CLI-description)
			- [**CLI Chapter 3:** Command Types](https://customersupport.septentrio.com/s/article/CLI-types)
			- [**CLI Chapter 4:** Command Line Syntax](https://customersupport.septentrio.com/s/article/CLI-syntax)
			- [**CLI Chapter 5:** Command Replies](https://customersupport.septentrio.com/s/article/CLI-replies)
			- [**CLI Chapter 6:** Command Syntax Tables](https://customersupport.septentrio.com/s/article/CLI-syntax-tables)
			- [**CLI Chapter 7:** Where can I find the list of all the commands supported by my receiver?](https://customersupport.septentrio.com/s/article/CLI-supported-commands)
			- [Generating a Diagnostic Report via Script or Command Line](https://customersupport.septentrio.com/s/article/Generating-a-diagnostic-report-via-Script-or-Command-Line)
	- [Learn More](https://www.septentrio.com/en/learn-more)
		- [Webinars](https://www.septentrio.com/en/learn-more/webinars)
		- [Technical Papers](https://www.septentrio.com/en/learn-more/technical-papers)
		- [Insights](https://www.septentrio.com/en/learn-more/insights) *(Case Studies and Technical Articles)*
		- [Community](https://www.septentrio.com/en/learn-more/community)
		- [Agnostic Corrections Program](https://www.septentrio.com/en/products/correction-services/precise-point-positioning-services-land/agnostic-corrections-program-gnss-correction-services)
- [JammerTest - Anti-Jamming and Anti-Spoofing Performance](https://www.septentrio.com/en/learn-more/insights/most-resilient-gnss-receiver-results-jammertest-norway)

Feyman Inc. also provides some resources for the IM19 attitude module:

- :material-web: [IM19 Product Page](https://global.feymani.com/product/attitede/im19ee/)
	- :material-newspaper-variant: [Documentation](https://global.feymani.com/document/)
- :material-web: [IM19 Product Page](http://feymani.com/en/show-53-2-1.html) *(alternate website)*
- :material-youtube: [Feyman Inc. YouTube Channel](https://www.youtube.com/@FeymanIncFMI)
