sparkfun/SparkFun_GNSS_Flex_System/flex_boards/SparkPNT_GNSS_Flex_Module_mosaic-X5-Tilt/docs/resources.md

## Product Resources

- Product Pages
	- :sfe: [SparkPNT GNSS Flex Module - mosaic-X5 & IM19](https://www.sparkfun.com/sparkpnt-gnss-flex-module-mosaic-x5-im19-imu.html)
	- :sfe: [SparkFun GNSS Flex pHAT - mosaic-X5 & IM19](https://www.sparkfun.com/sparkpnt-gnss-flex-phat-mosaic-x5-im19-imu.html)
- :material-folder-cog: Design Files:
	- :fontawesome-solid-file-pdf: [Schematic](./assets/board_files/schematic.pdf)
	- :fontawesome-solid-file-pdf: [Board Dimensions](./assets/board_files/dimensions.pdf)
	- :material-folder-zip: [KiCad Files](./assets/board_files/kicad_files.zip)
	- :material-cube-outline: [STEP File](./assets/3d_model/cad_model.step)
- Component Documentation
	- mosaic-X5 GNSS Receiver
		- :fontawesome-solid-file-pdf: [mosaic-X5 Datasheet](./assets/component_documentation/mosaic_hardware_manual_v1.11.0.pdf)
		- :fontawesome-solid-file-pdf: [mosaic-X5 Brochure](./assets/component_documentation/Septentrio_mosaic-X5_LR.pdf)
		- :fontawesome-solid-file-pdf: [Firmware Manual *(v4.15.0)*](./assets/component_documentation/firmware/mosaic-X5_Firmware_v4.15.0_Reference_Guide.pdf)
	- IM19 Attitude Module
		- :fontawesome-solid-file-pdf: [Datasheet](../assets/component_documentation/IM19.pdf)
		- :fontawesome-solid-file-pdf: [Integration Guide](../assets/component_documentation/IM19EI_v1.4.1.pdf)
- :material-github: [GitHub Repository](https://github.com/sparkfun/SparkFun_GNSS_Flex_System)

## 🏭&nbsp;Manufacturer's Resources
Septentrio also provides great resources for the mossaic-X5 GNSS receiver:

- [mosaic-X5 Product Page](https://www.septentrio.com/en/products/gps/gnss-receiver-modules/mosaic-x5)
- :material-youtube: [Septentrio YouTube Channel](https://www.youtube.com/channel/UCrA9wMw1y1f-KeOnnhq4lrA/feed)
- [Support Page](https://www.septentrio.com/en/support)
	- :material-head-question: [Technical Support Portal](https://customersupport.septentrio.com/s/)
		- :material-head-lightbulb: [Knowledge Base](https://customersupport.septentrio.com/s/topiccatalog)
	- [Learn More](https://www.septentrio.com/en/learn-more)
		- [Webinars](https://www.septentrio.com/en/learn-more/webinars)
		- [Technical Papers](https://www.septentrio.com/en/learn-more/technical-papers)
		- [Insights](https://www.septentrio.com/en/learn-more/insights) *(Case Studies and Technical Articles)*
		- [Community](https://www.septentrio.com/en/learn-more/community)
		- [Agnostic Corrections Program](https://www.septentrio.com/en/products/correction-services/precise-point-positioning-services-land/agnostic-corrections-program-gnss-correction-services)
- [JammerTest 2023 - Anti-Jamming and Anti-Spoofing Performance](https://www.septentrio.com/en/learn-more/insights/most-resilient-gnss-receiver-results-jammertest-norway)

Feyman Inc. also provides some resources for the IM19 attitude module:

- :material-web: [IM19 Product Page](https://global.feymani.com/product/attitede/im19ee/)
	- :material-newspaper-variant: [Documentation](https://global.feymani.com/document/)
- :material-web: [IM19 Product Page](http://feymani.com/en/show-53-2-1.html) *(alternate website)*
- :material-youtube: [Feyman Inc. YouTube Channel](https://www.youtube.com/@FeymanIncFMI)
