sparkfun/SparkFun_GNSS_Flex_System/flex_boards/SparkPNT_GNSS_Flex_Module_ZED-X20P-Tilt/docs/resources.md

## Product Resources

<div class="grid" markdown>

<div markdown>

- Product Pages
	- :sfe: [SparkPNT GNSS Flex Module - ZED-X20P](https://www.sparkfun.com/sparkpnt-gnss-flex-module-zed-x20p.html)
	- :sfe: [SparkPNT GNSS Flex Module - ZED-X20P & IM19](https://www.sparkfun.com/sparkpnt-gnss-flex-module-zed-x20p-im19-imu.html)
	- :sfe: [SparkFun GNSS Flex pHAT - ZED-X20P](https://www.sparkfun.com/sparkfun-gnss-flex-phat-zed-x20p.html)
	- :sfe: [SparkFun GNSS Flex pHAT - ZED-X20P & IM19](https://www.sparkfun.com/sparkfun-gnss-flex-phat-zed-x20p-im19-imu.html)
- :material-folder-cog: Design Files:
	- :fontawesome-solid-file-pdf: [Board Dimensions](./assets/board_files/dimensions.pdf)
	- :fontawesome-solid-file-pdf: [Schematic](./assets/board_files/schematic.pdf)
	- :material-folder-zip: [KiCad Files](./assets/board_files/kicad_files.zip)
	- :material-cube-outline: [STEP File](./assets/3d_model/cad_model.step)
- :fontawesome-solid-computer: [u-center 2 Software](https://www.u-blox.com/en/product/u-center)
	- :material-cloud-download: [Download](https://u-center2-updates.u-blox.com/u-center2-installer.exe)
	- :material-book-open-variant: [User Manual](https://www.u-blox.com/en/info/u-center-2-user-guide)

</div>

<div markdown>

- Component Documentation
	- ZED-X20P GNSS Receiver
		- :fontawesome-solid-file-pdf: [Datasheet](https://www.u-blox.com/sites/default/files/documents/ZED-X20P-00B_DataSheet_UBXDOC-963802114-12690.pdf)
		- :fontawesome-solid-file-pdf: [Product Summary](https://www.u-blox.com/sites/default/files/documents/ZED-X20P_ProductSummary_UBXDOC-304424225-18238.pdf)
		- :fontawesome-solid-file-pdf: [Integration Manual](https://www.u-blox.com/sites/default/files/documents/ZED-X20P_IntegrationManual_UBXDOC-963802114-12901.pdf)
		- Application Notes
			- :fontawesome-solid-file-pdf: [GPS L5 Configuration](https://www.u-blox.com/sites/default/files/documents/GPS-L5-configuration_AppNote_UBX-21038688.pdf)
		- Firmware *(HPG 2.02)*
			- :octicons-file-binary-16: [Firmware File](https://content.u-blox.com/sites/default/files/2025-07/UBX_20_HPG_202_ZED_F20P.329facb56ce18631d607fe15177834dc.bin)
			- :fontawesome-solid-file-pdf: [Interface Manual](https://content.u-blox.com/sites/default/files/documents/u-blox-X20-HPG-2.02_InterfaceDescription_UBXDOC-304424225-19967.pdf)
			- :fontawesome-solid-file-pdf: [Release Notes](https://content.u-blox.com/sites/default/files/documents/HPG202_RN_UBXDOC-304424225-20040.pdf)
	- IM19 Attitude Module
		- :fontawesome-solid-file-pdf: [Datasheet](../assets/component_documentation/IM19.pdf)
		- :fontawesome-solid-file-pdf: [Integration Guide](../assets/component_documentation/IM19EI_v1.4.1.pdf)
- :material-github: [GitHub Repository](https://github.com/sparkfun/SparkFun_GNSS_Flex_System)

</div>

</div>

## 🏭&nbsp;Manufacturer's Resources
u-blox also provides great resources for the ZED-X20P GNSS receiver:

- :material-web: [ZED-X20P Product Page](https://www.u-blox.com/en/product/zed-x20p-module)
- :material-youtube: [u-blox YouTube Channel](https://www.youtube.com/@ublox)
	- :material-playlist-play: [Playlist: u-center 2](https://www.youtube.com/playlist?list=PLSzSoRUA4EXuo9NTsbTnK84MiKvbVCEKt)
- :material-head-question: [Support Page](https://portal.u-blox.com/s/)
- :material-folder-information: [Product Documentation](https://www.u-blox.com/en/product-resources?legacy=Current)
	- :material-head-lightbulb: [PNT Technologies](https://www.u-blox.com/en/positioning-and-location)
	- :material-head-lightbulb: [High Precision Positioning](https://www.u-blox.com/en/technologies/high-precision-positioning)
	- [u-center 2 Software](https://www.u-blox.com/en/product/u-center)
		- [u-center 2 User Manual](https://www.u-blox.com/en/info/u-center-2-user-guide)
		- [Tutorials](https://www.u-blox.com/en/u-center2-tutorials)

Feyman Inc. also provides some resources for the IM19 attitude module:

- :material-web: [IM19 Product Page](https://global.feymani.com/product/attitede/im19ee/)
	- :material-newspaper-variant: [Documentation](https://global.feymani.com/document/)
- :material-web: [IM19 Product Page](http://feymani.com/en/show-53-2-1.html) *(alternate website)*
- :material-youtube: [Feyman Inc. YouTube Channel](https://www.youtube.com/@FeymanIncFMI)
