sparkfun/SparkFun_GNSS_Flex_System/docs/assets/3d_model/README.md

3d_model directory
====================
This folder should contain the 3D model of the product

## Solder Mask - Color Correction Values
Hex: #E0311D
RGB: 224, 49, 29

## 3D Model

### File Optimizer
https://www.loci-labs.com/optimizer

### Model Editor
https://modelviewer.dev/editor/

## 3D Animation

### Blockbench
https://web.blockbench.net/

### GLTF to GLB Converte
https://convert3d.org/app?r=gltf-to-glb

### File Optimizer
https://glb.babylonpress.org/
