sparkfun/SparkFun_GNSS_Flex_System/docs/assets/3d_model/poster-carrier_board.png

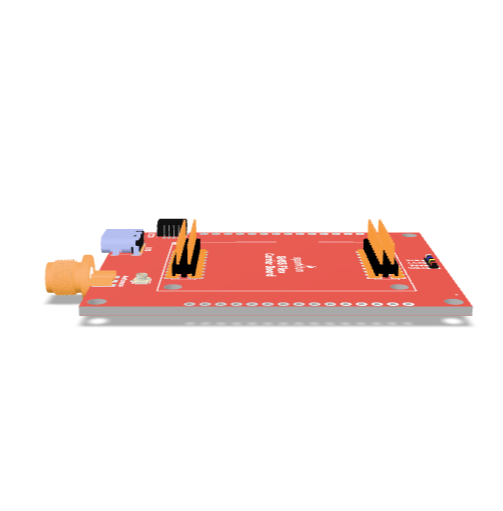
docs/assets/3d_model/poster-carrier_board.png
