sparkfun/SparkFun_GNSS_Flex_System/docs/assets/3d_model/poster-generic_module.png

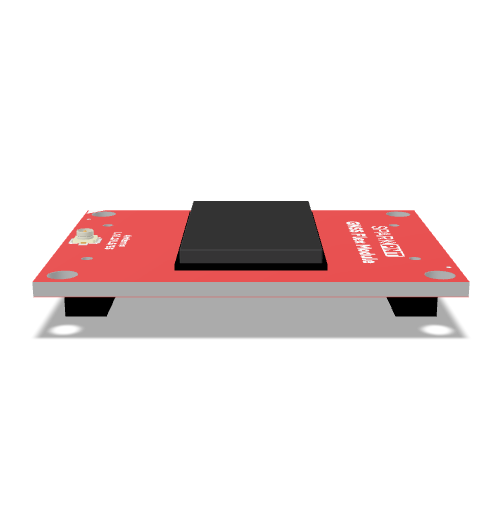
docs/assets/3d_model/poster-generic_module.png
