sparkfun/SparkFun_GNSS_Flex_System/docs/assets/img/hookup_guide/module-pinout.png

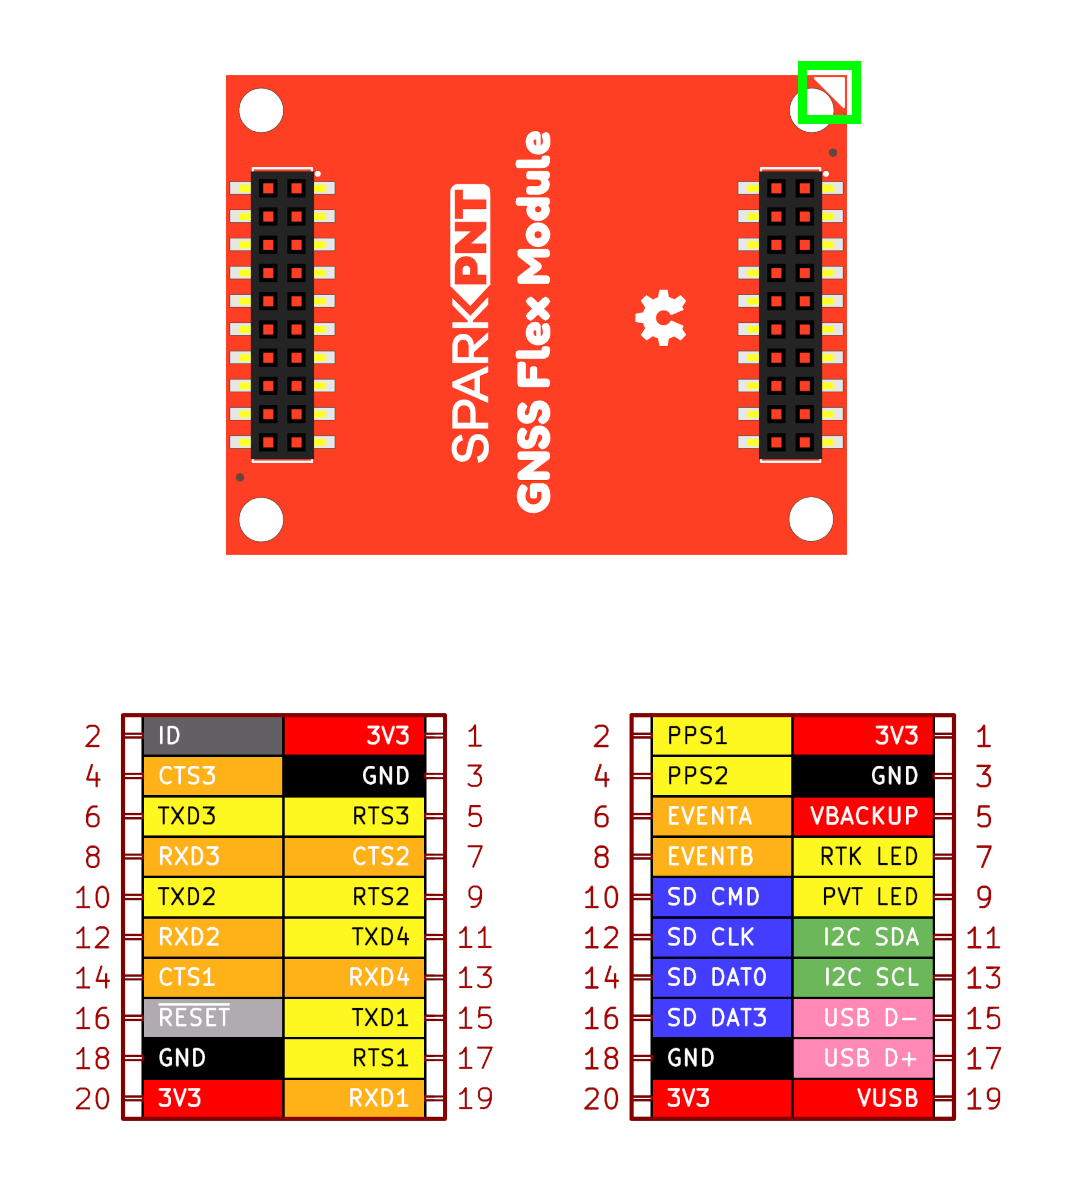
docs/assets/img/hookup_guide/module-pinout.png
