sparkfun/SparkFun_GNSS_Flex_System/docs/assets/img/thumbnail.jpg

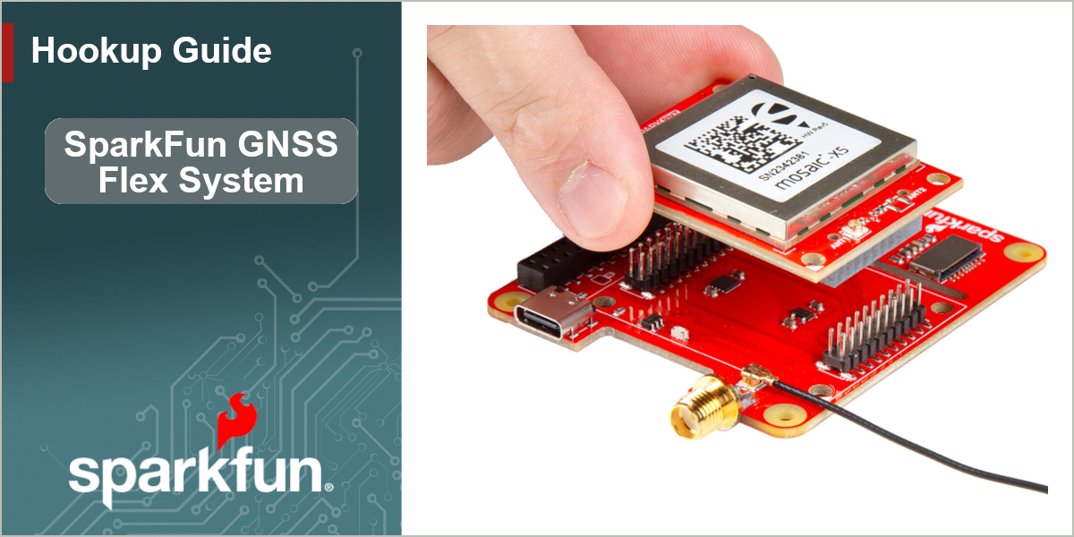
docs/assets/img/thumbnail.jpg
