sparkfun/SparkFun_GNSS_Flex_System/flex_boards/SparkPNT_GNSS_Flex_Module_LG290P-Tilt/hardware/Dimensions.png

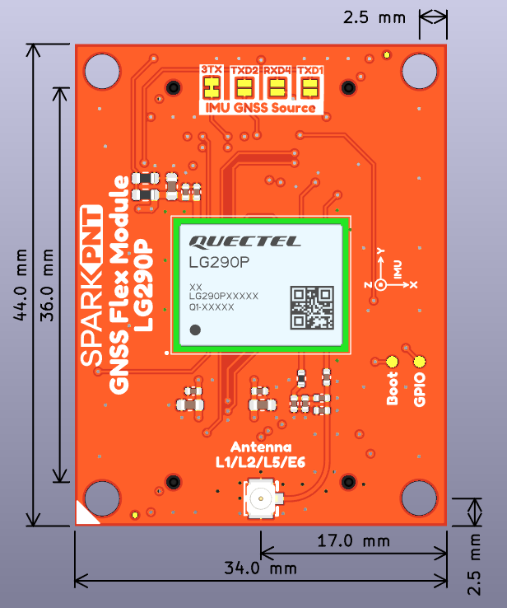
flex_boards/SparkPNT_GNSS_Flex_Module_LG290P-Tilt/hardware/Dimensions.png
