sparkfun/SparkFun_GNSS_Flex_System/flex_boards/SparkPNT_GNSS_Flex_Module_mosaic-X5-Tilt/docs/assets/3d_model/poster.png

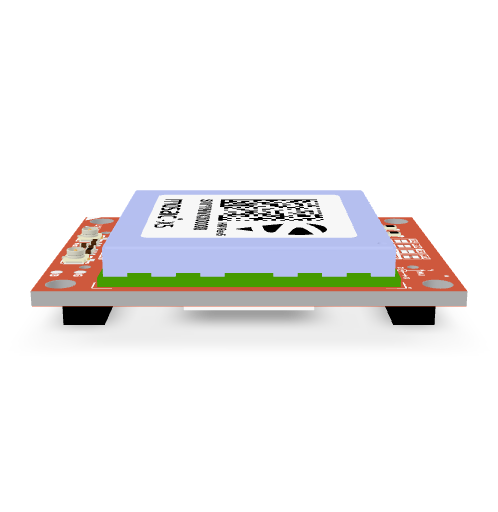
flex_boards/SparkPNT_GNSS_Flex_Module_mosaic-X5-Tilt/docs/assets/3d_model/poster.png
