sparkfun/SparkFun_GNSS_Flex_System/flex_boards/SparkPNT_GNSS_Flex_Module_LG290P-Tilt/docs/hardware_assembly.md

## GNSS Antenna
In order to receive [GNSS](https://en.wikipedia.org/wiki/Satellite_navigation "Global Navigation Satellite System") signals, users will need to connect a compatible antenna. For the best performance, we recommend users choose an active, L1/L2/L5/L6 GNSS antenna and utilize a low-loss cable.

### U.FL Connector
GNSS antennas are connected to the U.FL connector on the GNSS Flex board. For sturdier connections, users have the option to bridging the connection to the SMA connector on a Flex carrier board.

<figure markdown>
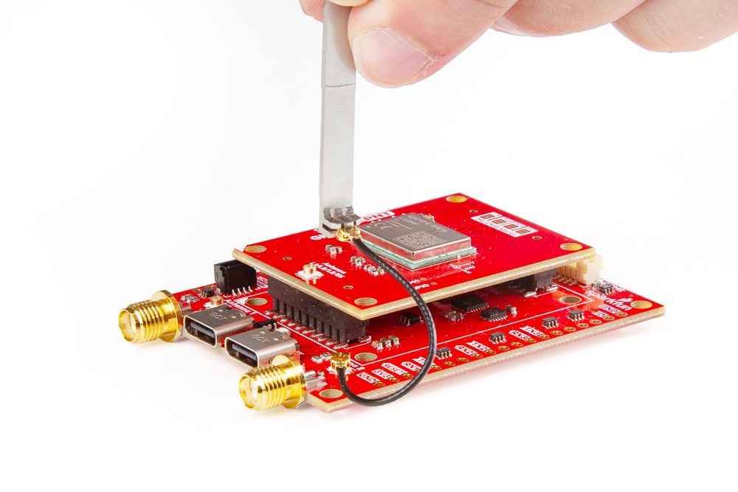
[picture p223: flex_boards/SparkPNT_GNSS_Flex_Module_LG290P-Tilt/docs/assets/img/hookup_guide/assembly-ufl.jpg]
Antenna connection

<figcaption markdown>Attaching an U.FL cable to the GNSS Flex board.</figcaption>
</figure>

!!! tip
	For the best performance, we recommend users choose a compatible L1/L2/L5/L6 GNSS antenna and utilize a low-loss cable. Also, don't forget that GNSS signals are fairly weak and can't penetrate buildings or dense vegetation. The GNSS antenna should have an unobstructed view of the sky.

## GNSS Flex Headers
SparkPNT GNSS Flex modules are *plug-in boards* featuring different GNSS receivers. They are designed to be easily swapped for repairs and pin-compatible for upgrades. The boards come populated with two 2x10 pin, 2mm pitch female headers for connecting to *carrier boards*.

<figure markdown>
Stacking LG290P GNSS Flex module onto a carrier board
<figcaption markdown>Stacking a GNSS Flex module onto a *carrier* board.</figcaption>
</figure>
