sparkfun/SparkFun_GNSS_Flex_System/docs/assets/img/hookup_guide/carrier-top.png

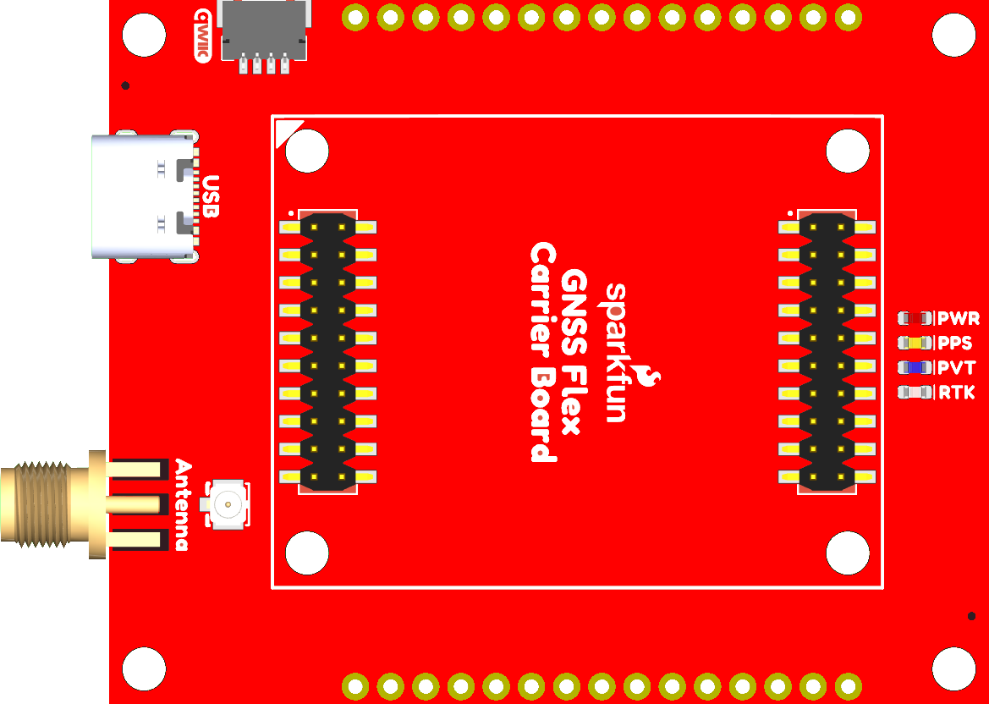
docs/assets/img/hookup_guide/carrier-top.png
