sparkfun/SparkFun_GNSS_Flex_System/docs/assets/img/hookup_guide/flex_module-bottom.png

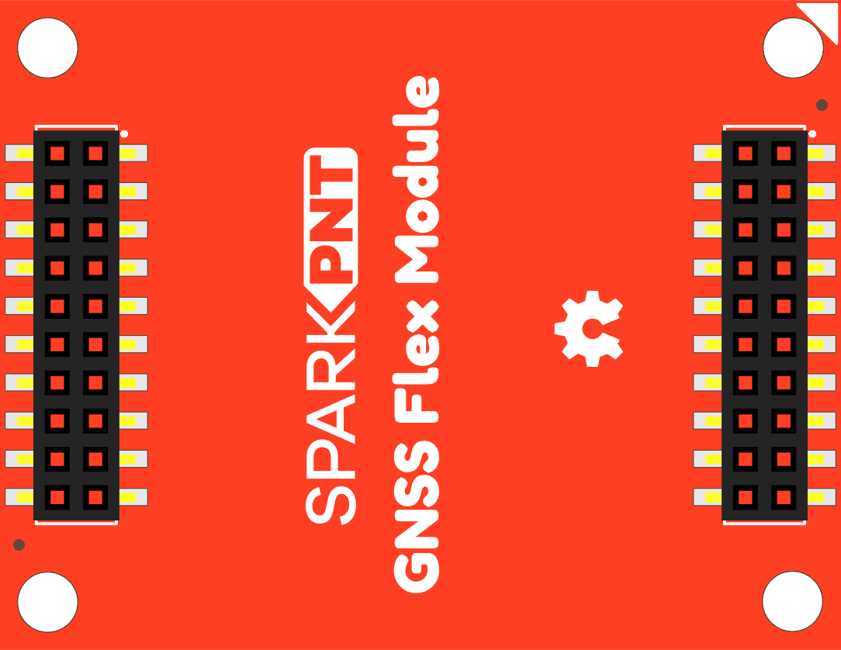
docs/assets/img/hookup_guide/flex_module-bottom.png
