sparkfun/SparkFun_GNSS_Flex_System/flex_boards/SparkPNT_GNSS_Flex_Module_DAN-F10N/docs/assets/img/hookup_guide/assembly-ufl.jpg

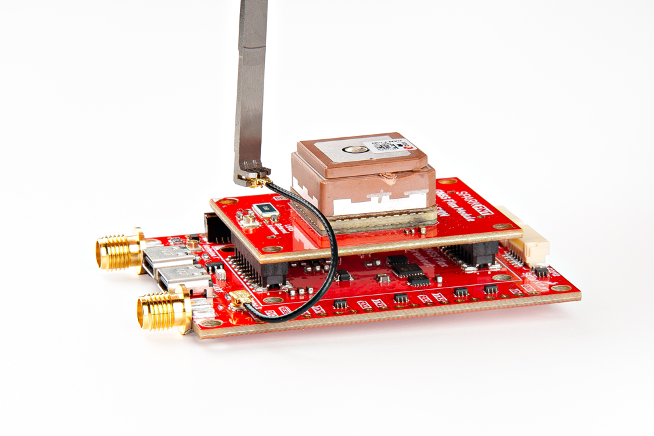
flex_boards/SparkPNT_GNSS_Flex_Module_DAN-F10N/docs/assets/img/hookup_guide/assembly-ufl.jpg
