sparkfun/SparkFun_GNSS_Flex_System/flex_boards/SparkPNT_GNSS_Flex_Module_LG290P/docs/assets/img/hookup_guide/orientation.png

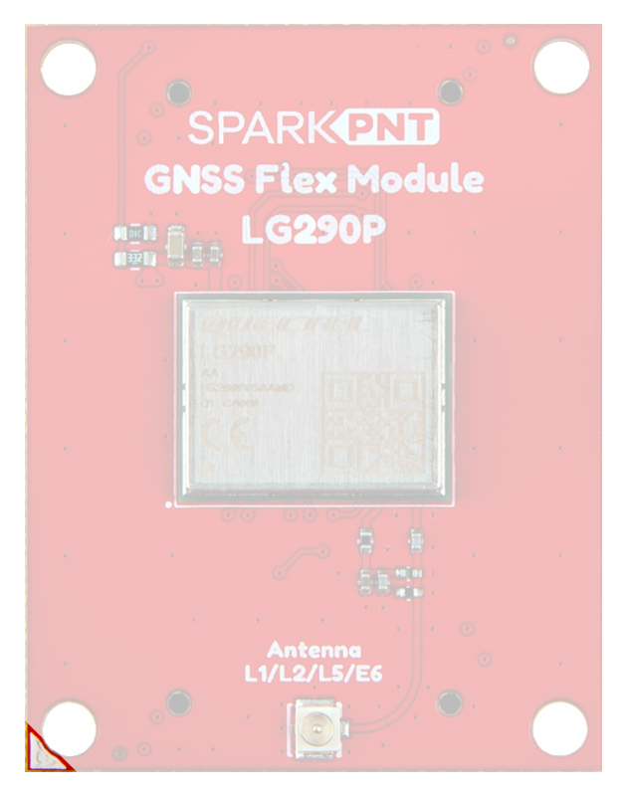
flex_boards/SparkPNT_GNSS_Flex_Module_LG290P/docs/assets/img/hookup_guide/orientation.png
