sparkfun/SparkFun_GNSS_Flex_System/flex_boards/SparkPNT_GNSS_Flex_Module_LG580P/docs/assets/img/hookup_guide/bottom-template.png

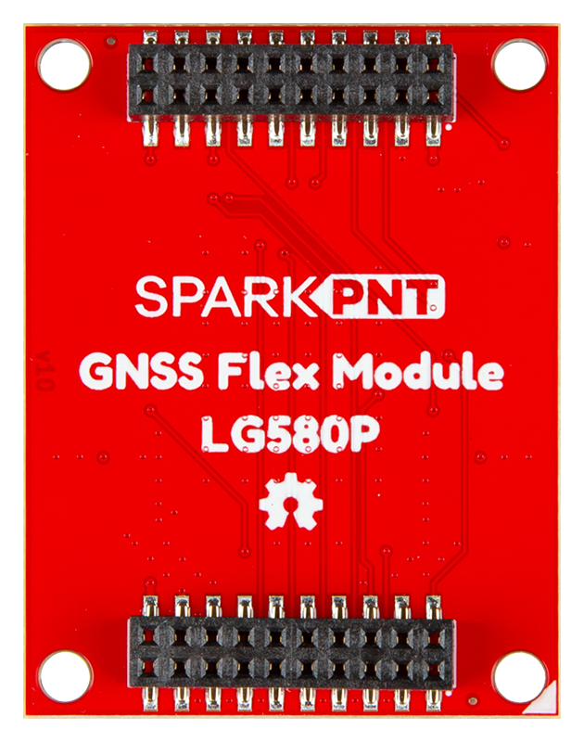
flex_boards/SparkPNT_GNSS_Flex_Module_LG580P/docs/assets/img/hookup_guide/bottom-template.png
