sparkfun/SparkFun_GNSS_Flex_System/flex_boards/SparkPNT_GNSS_Flex_Module_mosaic-X5/docs/assets/img/hookup_guide/bottom.png

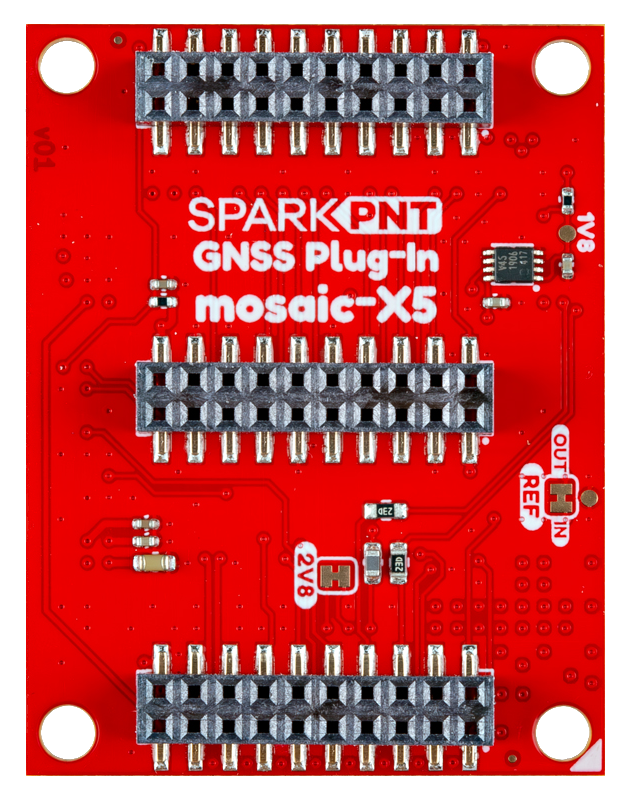
flex_boards/SparkPNT_GNSS_Flex_Module_mosaic-X5/docs/assets/img/hookup_guide/bottom.png
