sparkfun/SparkFun_GNSS_Flex_System/flex_boards/SparkPNT_GNSS_Flex_Module_ZED-X20P-Tilt/docs/assets/img/hookup_guide/bottom-template.png

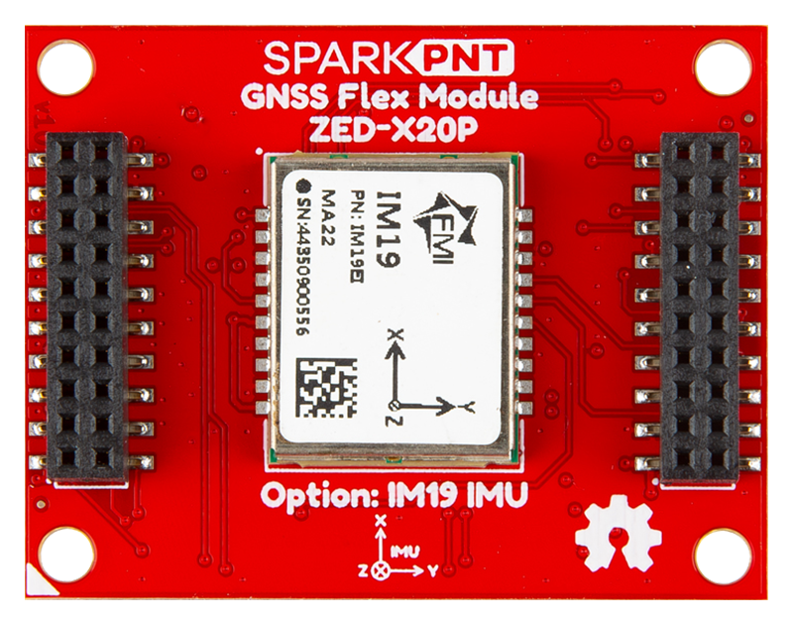
flex_boards/SparkPNT_GNSS_Flex_Module_ZED-X20P-Tilt/docs/assets/img/hookup_guide/bottom-template.png
