sparkfun/SparkFun_GNSS_Flex_System/flex_boards/template-SparkPNT_GNSS_Flex_Modules/docs/assets/img/hookup_guide/headers-flex_module.png

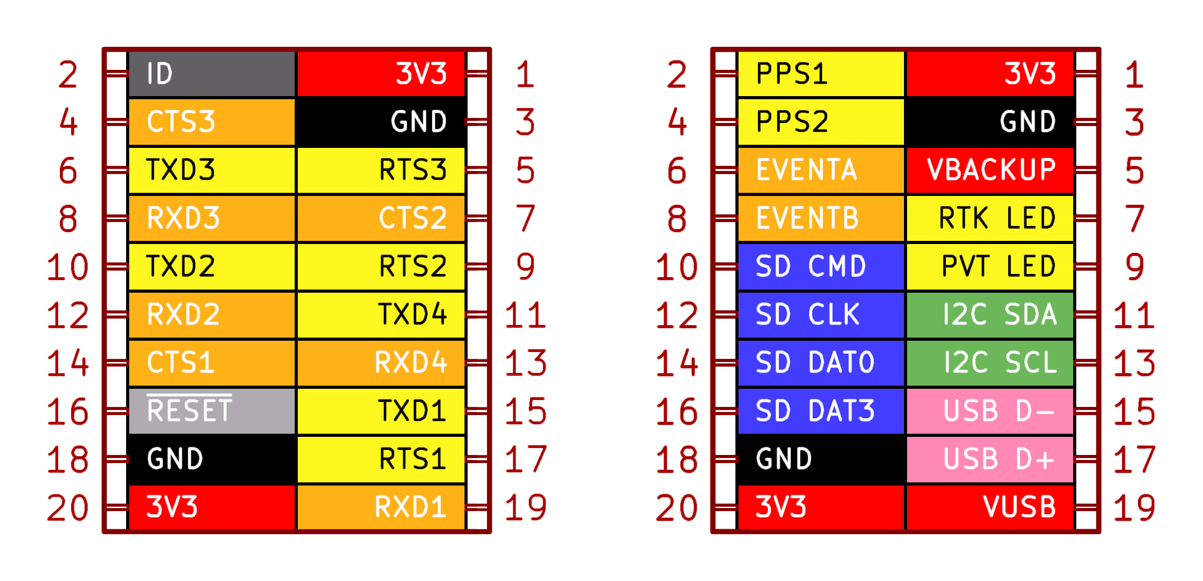
flex_boards/template-SparkPNT_GNSS_Flex_Modules/docs/assets/img/hookup_guide/headers-flex_module.png
