sparkfun/SparkFun_GNSS_Flex_System/flex_boards/SparkPNT_GNSS_Flex_Module_DAN-F10N/docs/assets/component_documentation/MAX-F10S_antennaSupervisor.pdf

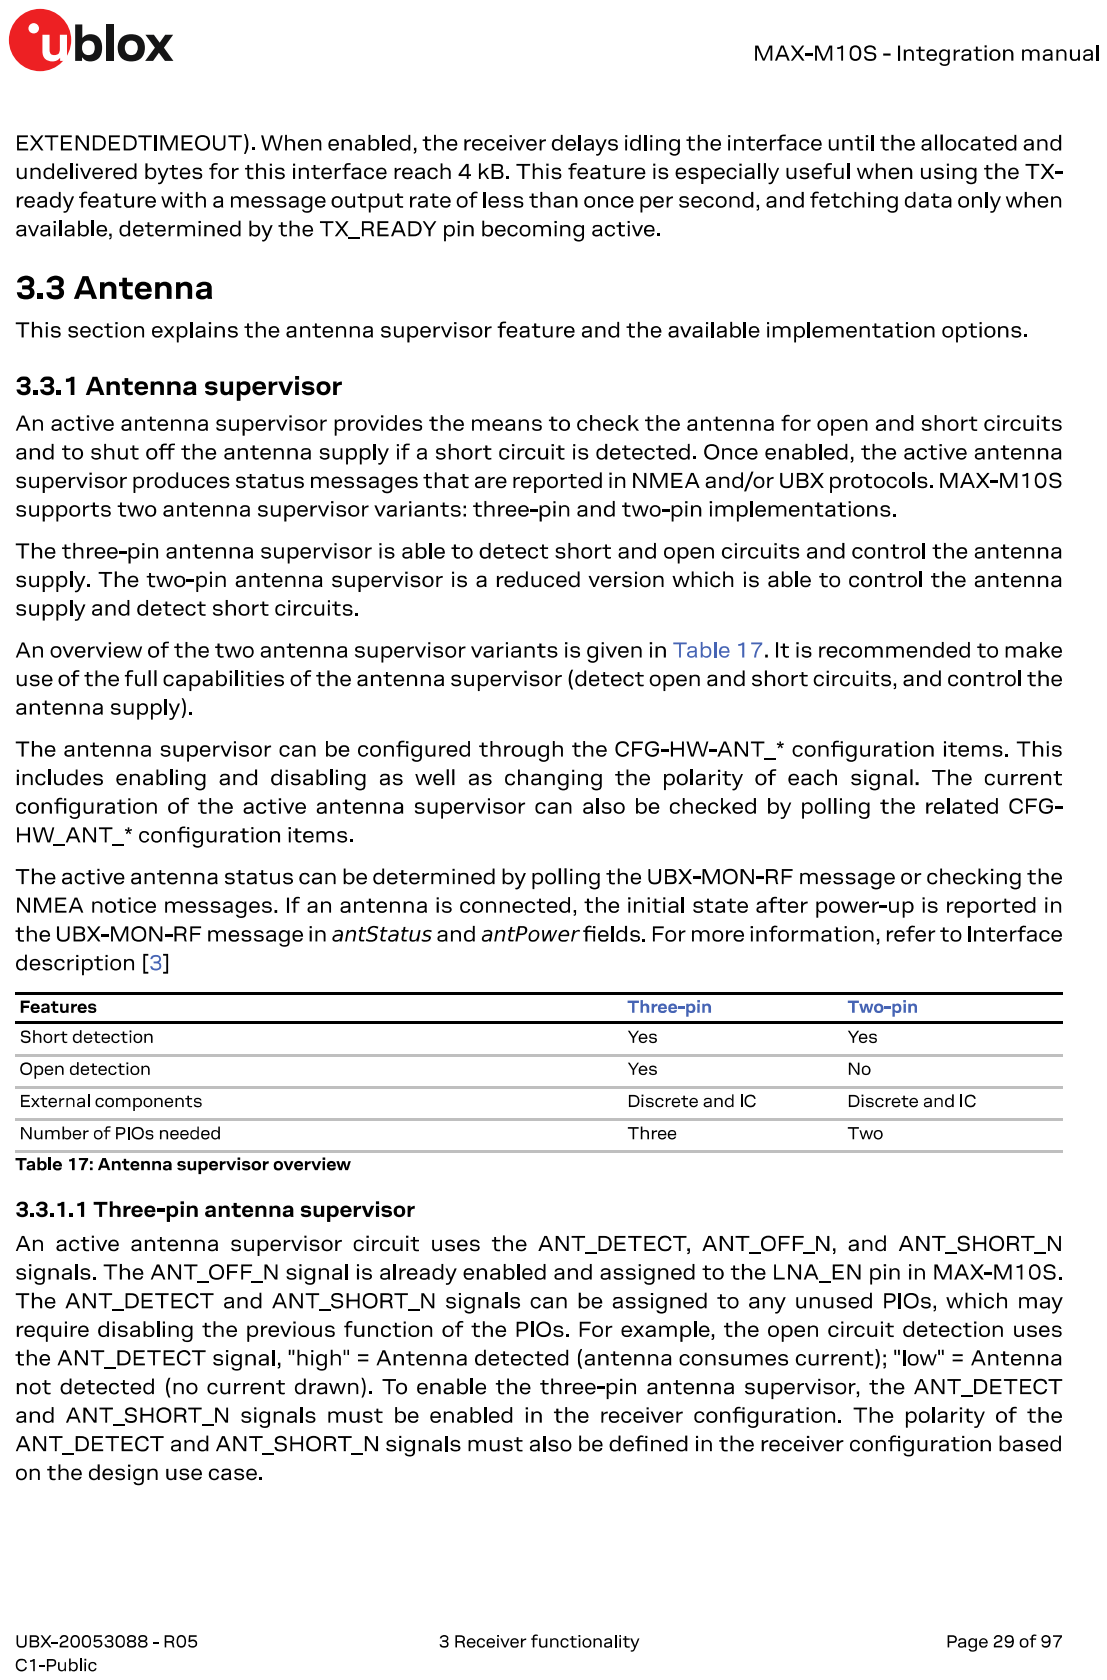
[picture p262: page 1]

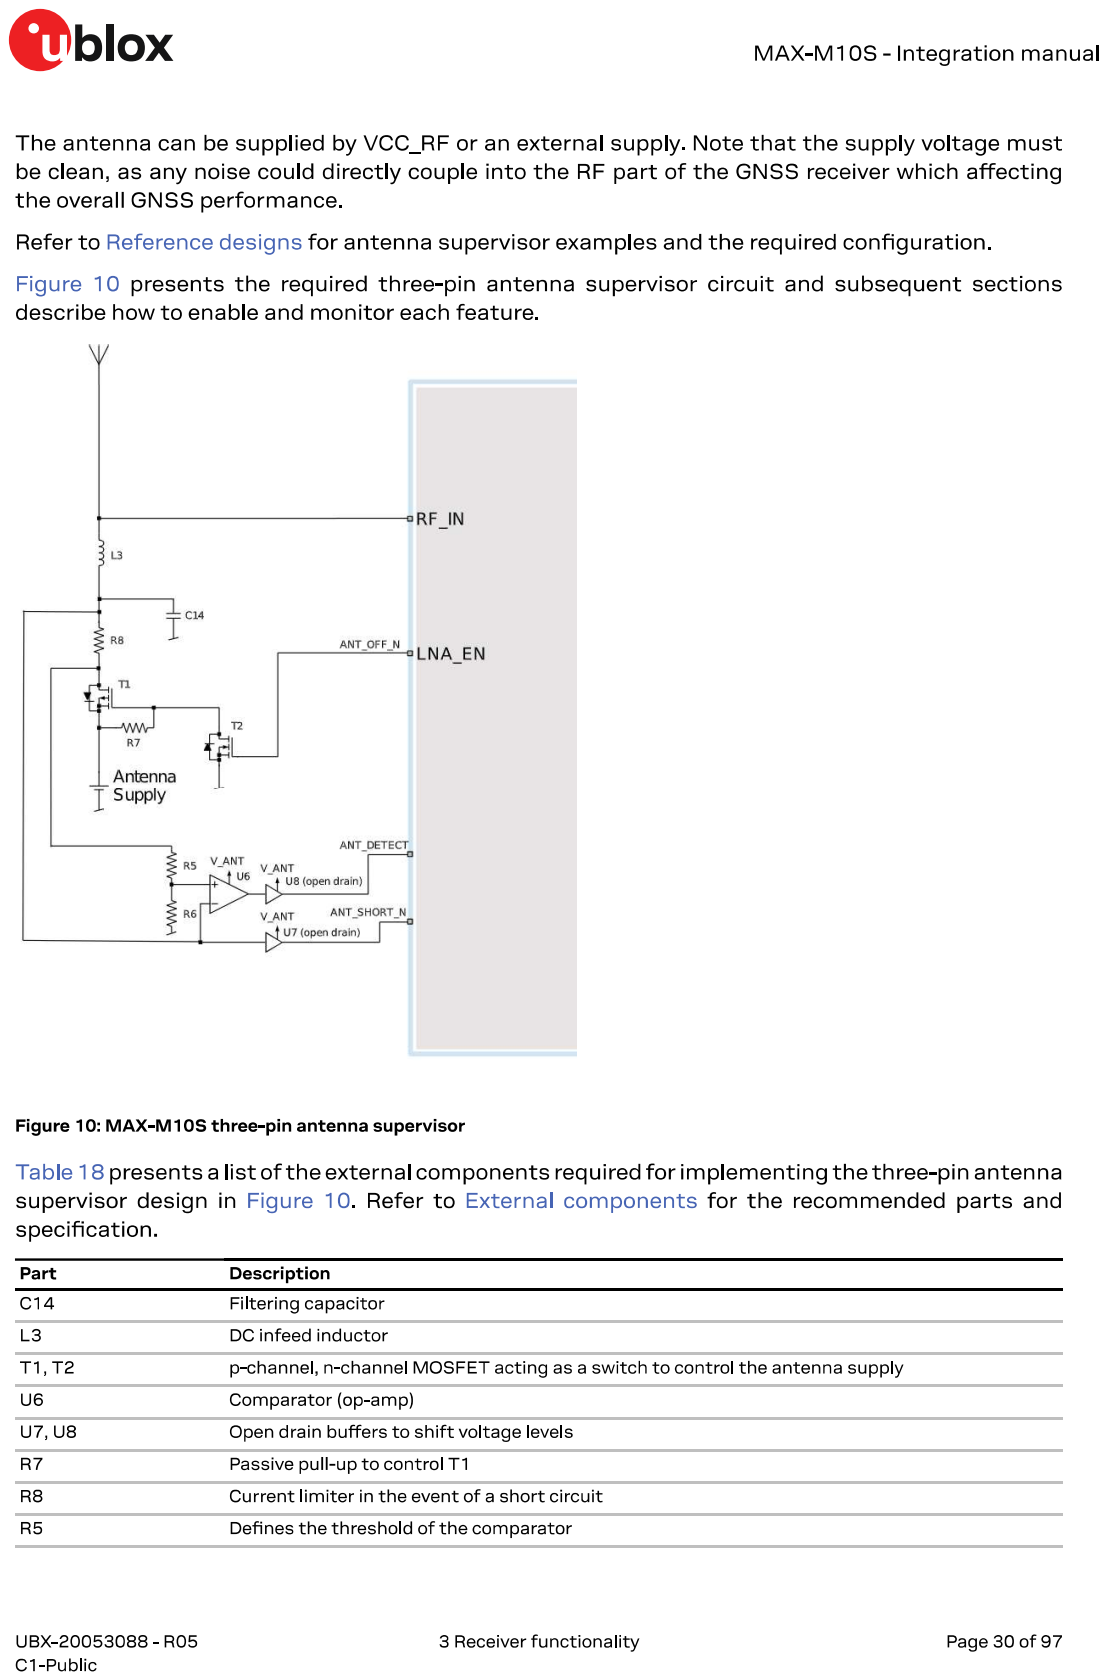
[picture p263: page 2]

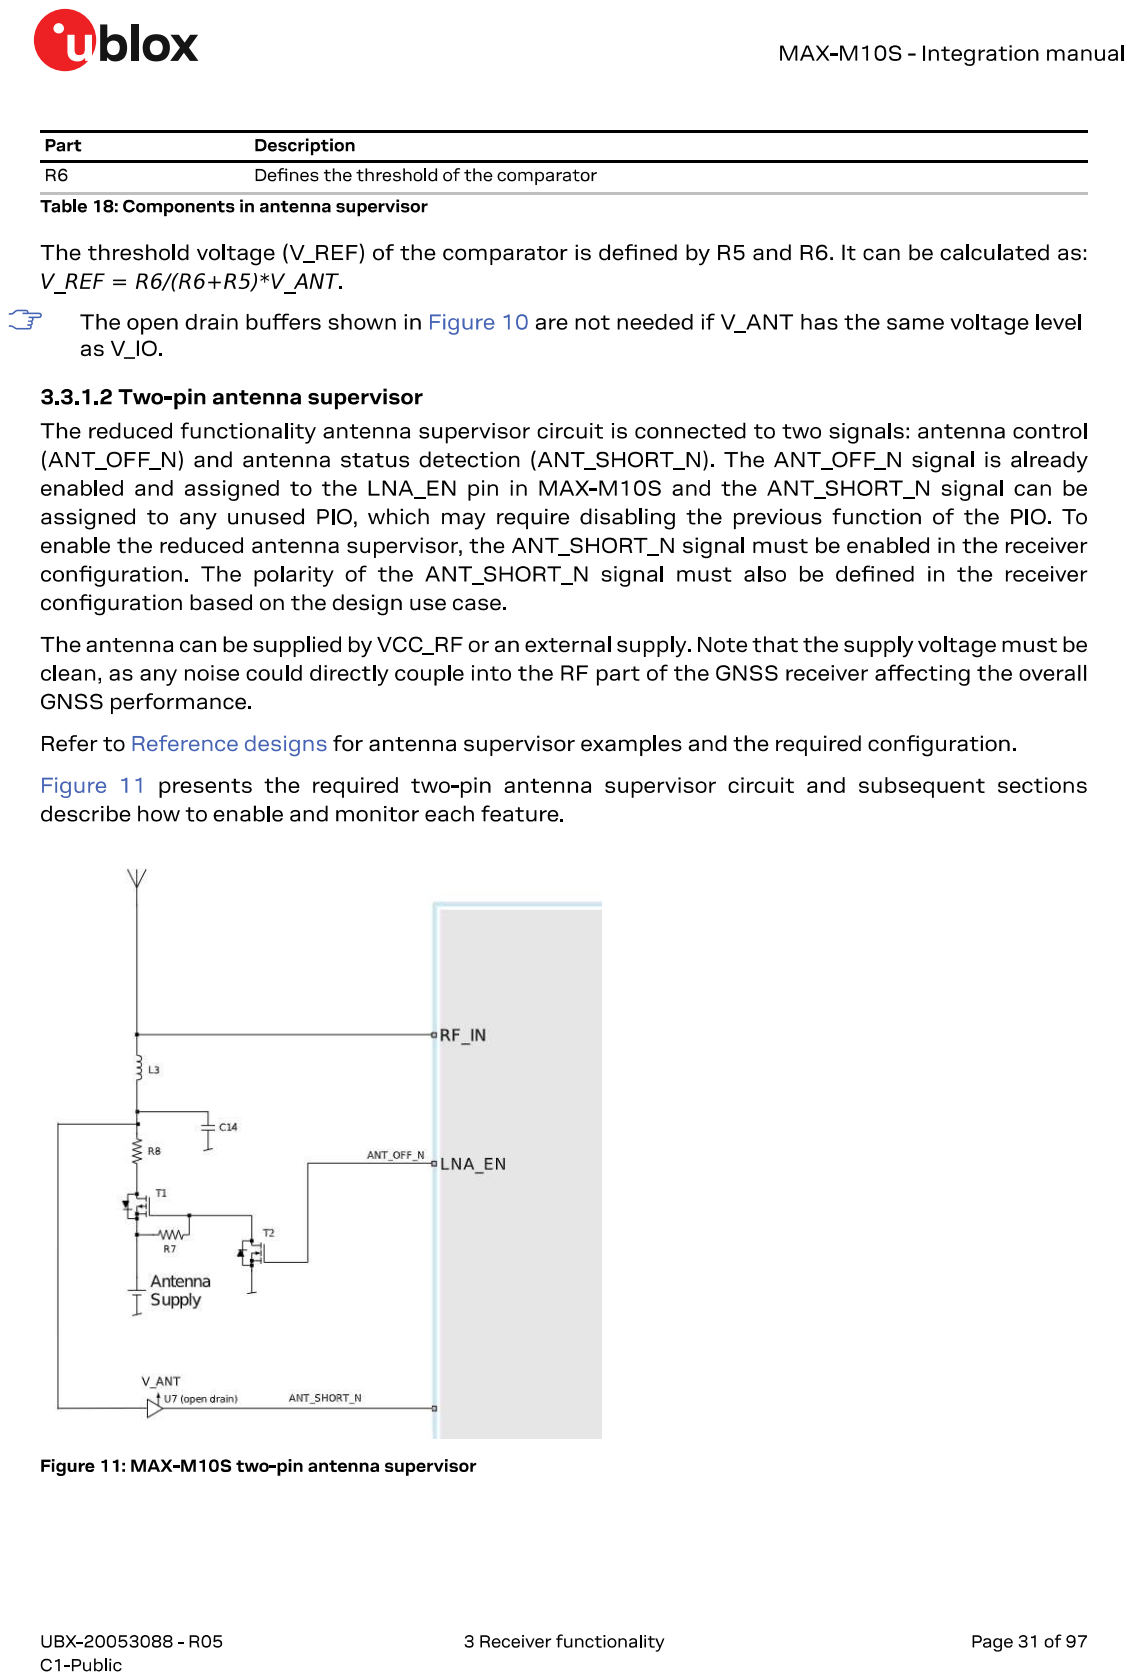
[picture p264: page 3]
