sparkfun/SparkFun_GNSS_Flex_System/flex_boards/SparkPNT_GNSS_Flex_Module_mosaic-X5-Tilt/docs/assets/board_files/dimensions.pdf

# 4.0 mm 17.0 mm

# 4.0 mm 17.0 mm

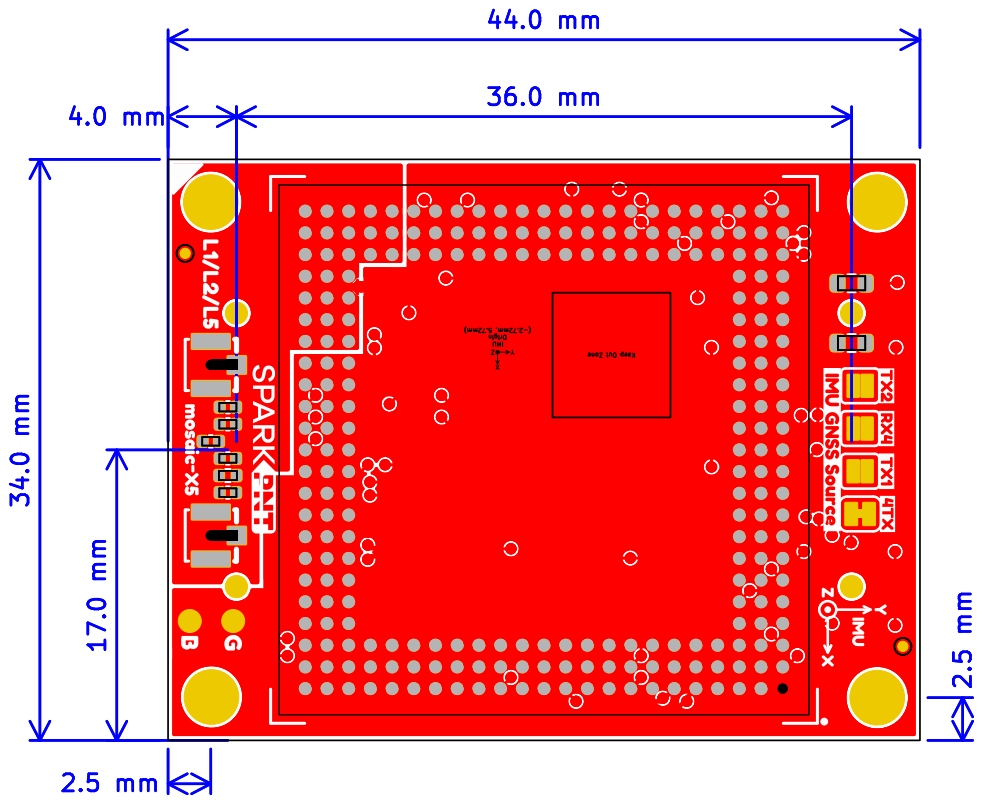
[picture p266: page 1]
