sparkfun/SparkFun_GNSS_Flex_System/flex_boards/SparkPNT_GNSS_Flex_Module_LG580P/docs/assets/board_files/dimensions.pdf

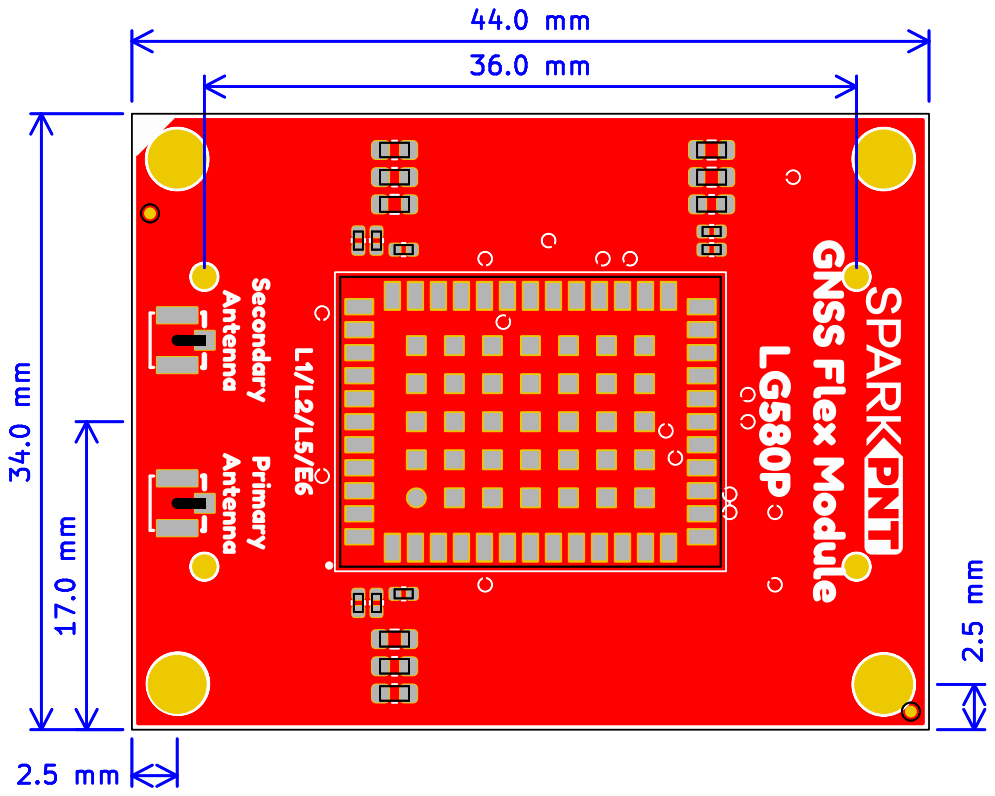
[picture p267: page 1]
2.5 mm¹⁷.0 mm
