sparkfun/SparkFun_GNSS_Flex_System/flex_boards/SparkPNT_GNSS_Flex_Module_LG290P-Tilt/docs/assets/board_files/dimensions.pdf

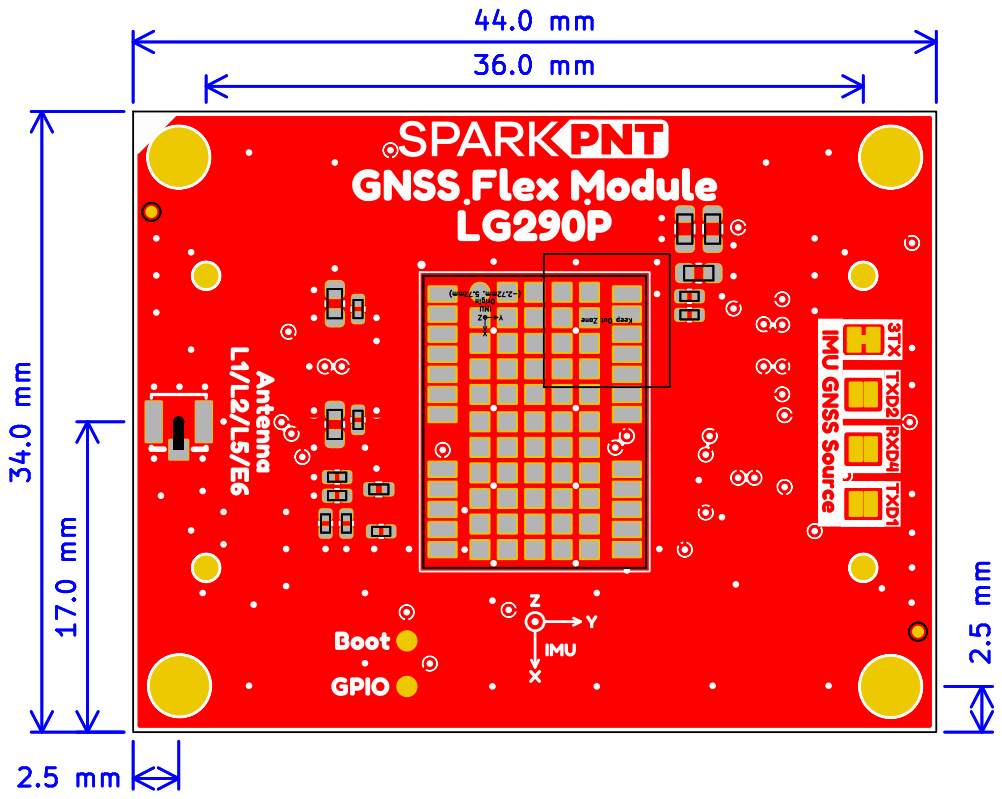
[picture p268: page 1]
2.5 mm¹⁷.0 mm
