sparkfun/SparkFun_GNSS_Flex_System/flex_boards/SparkPNT_GNSS_Flex_Module_LG580P/docs/assets/board_files/schematic.pdf

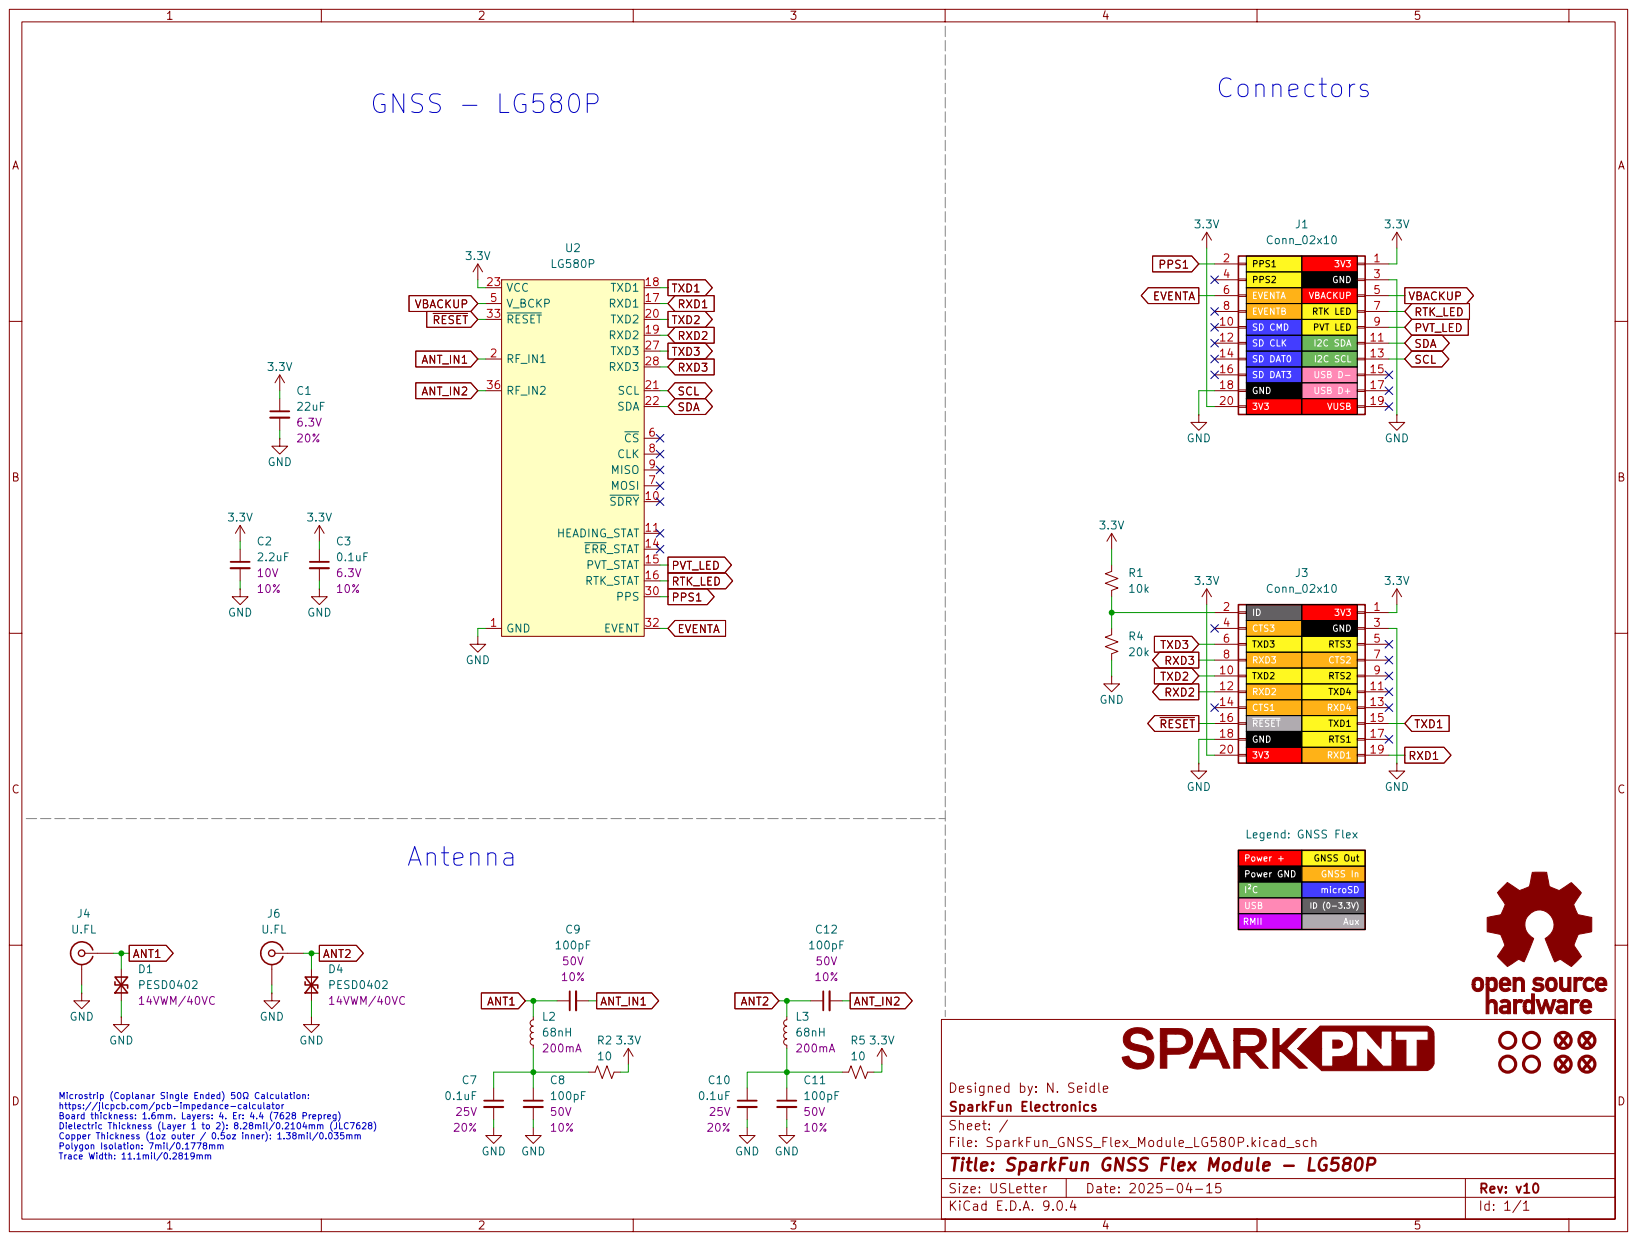
[picture p270: page 1]
