sparkfun/SparkFun_GNSS_Flex_System/flex_boards/SparkPNT_GNSS_Flex_Module_LG290P-Tilt/docs/assets/board_files/schematic.pdf

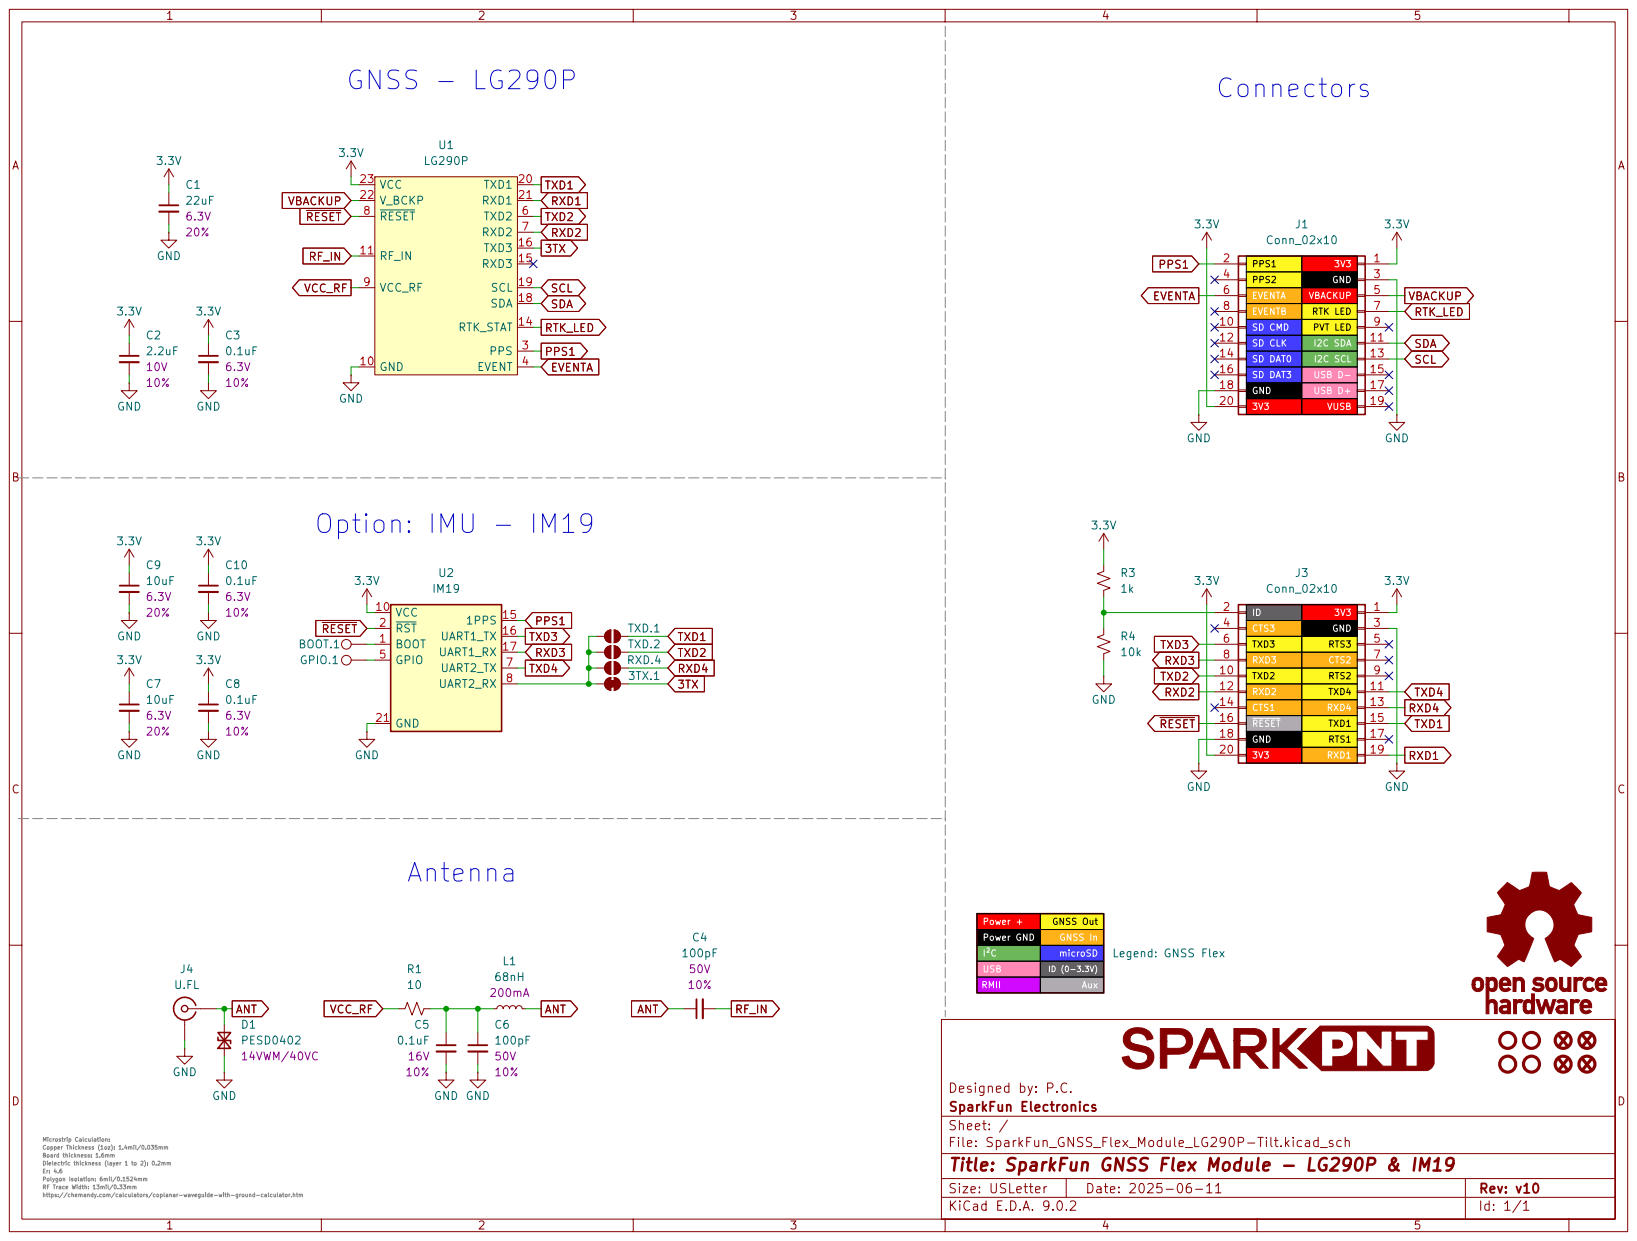
[picture p271: page 1]
