sparkfun/SparkFun_GNSS_Flex_System/flex_boards/SparkPNT_GNSS_Flex_Module_ZED-X20P-Tilt/docs/assets/board_files/dimensions.pdf

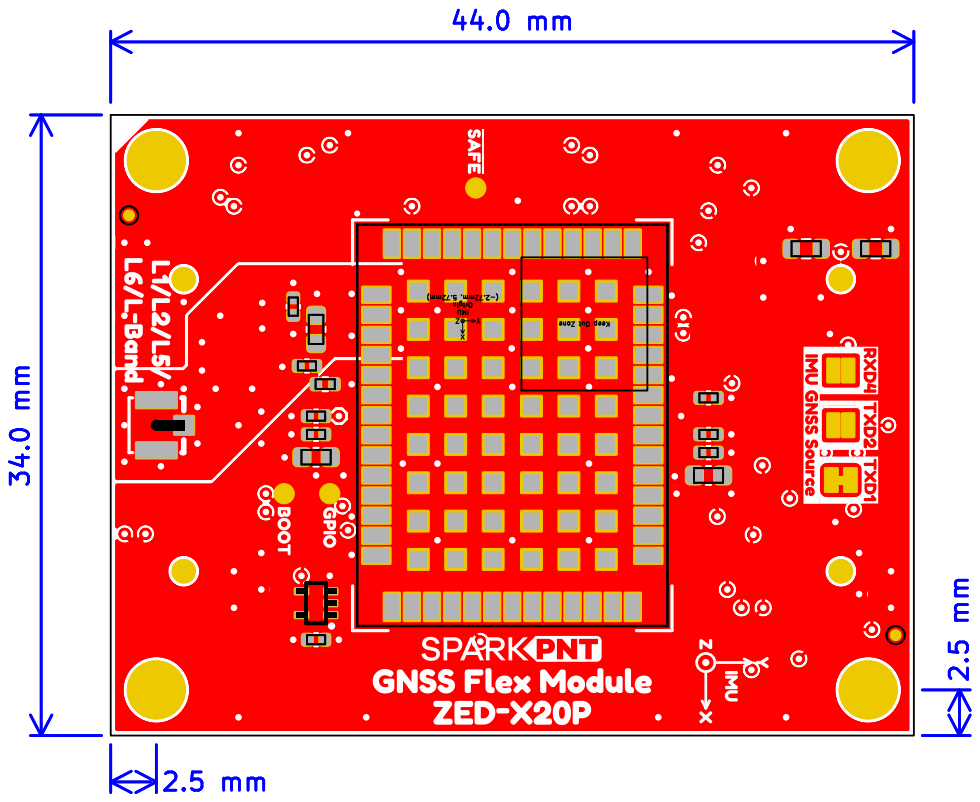
[picture p274: page 1]
