sparkfun/SparkFun_GNSS_Flex_System/flex_boards/SparkPNT_GNSS_Flex_Module_LG290P/docs/assets/board_files/dimensions.pdf

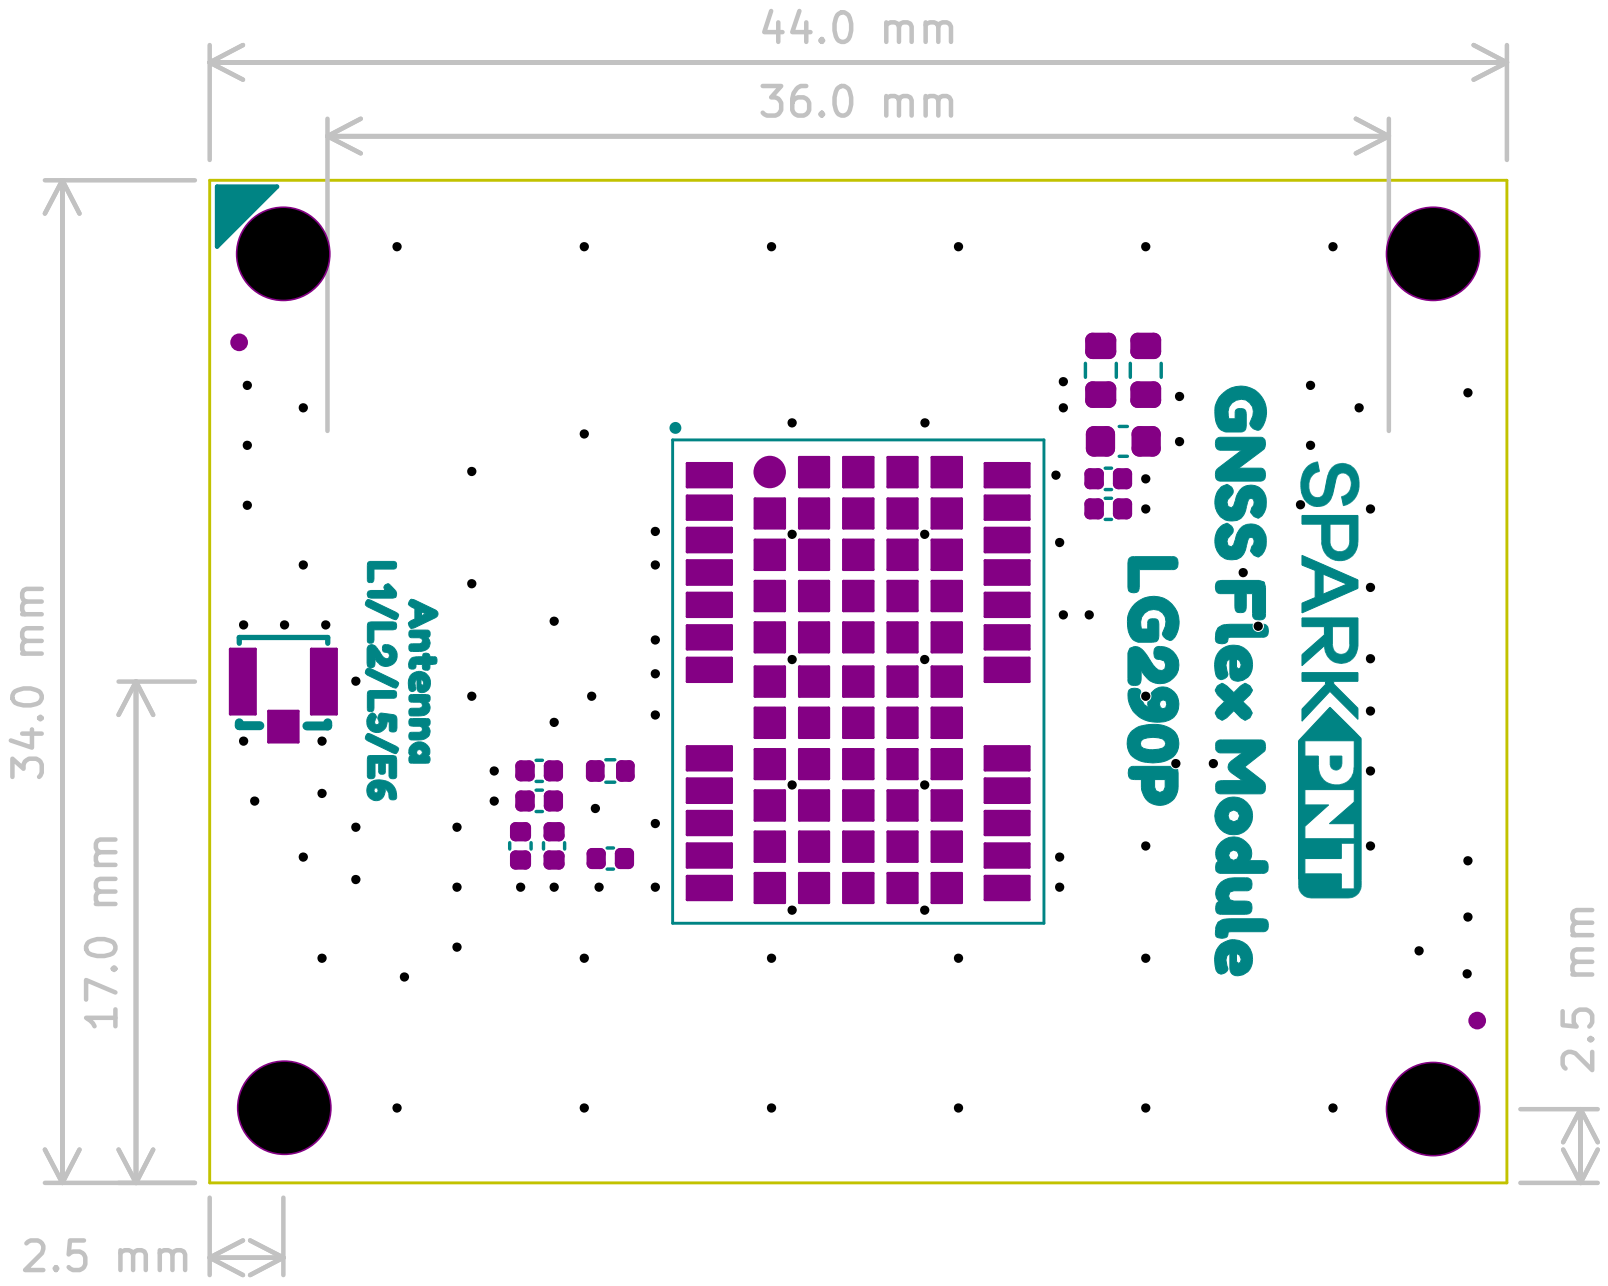
[picture p276: page 1]
